donnersm/EdisonRadio/Photos/IMG_9378.JPG

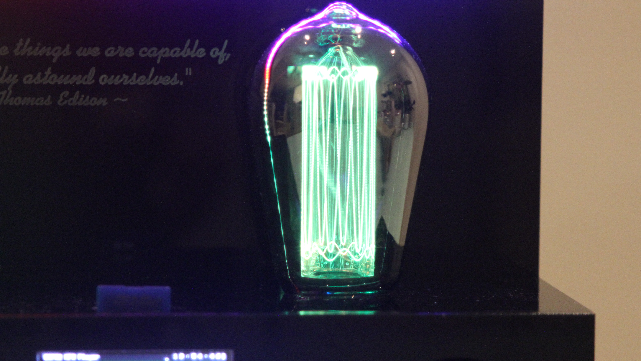
Photos/IMG_9378.JPG
