donnersm/EdisonRadio/Photos/IMG_9388.JPG

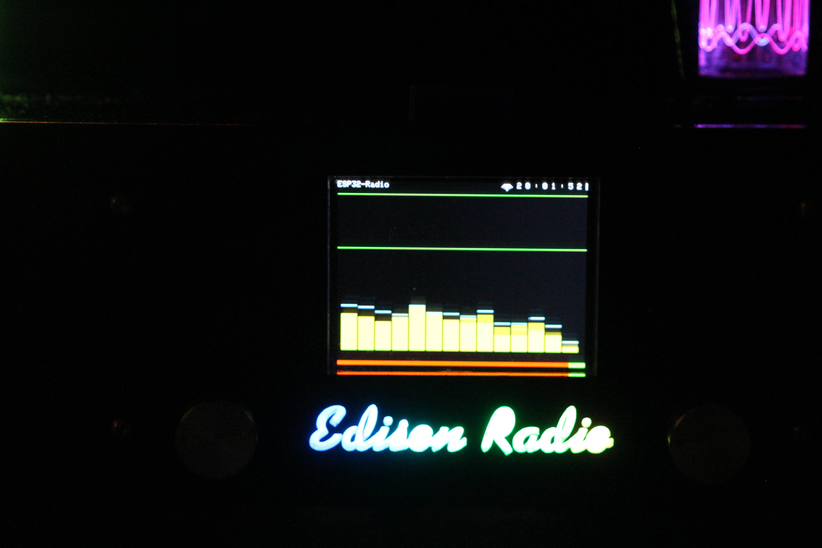
Photos/IMG_9388.JPG
