donnersm/EdisonRadio/Photos/IMG_9389.JPG

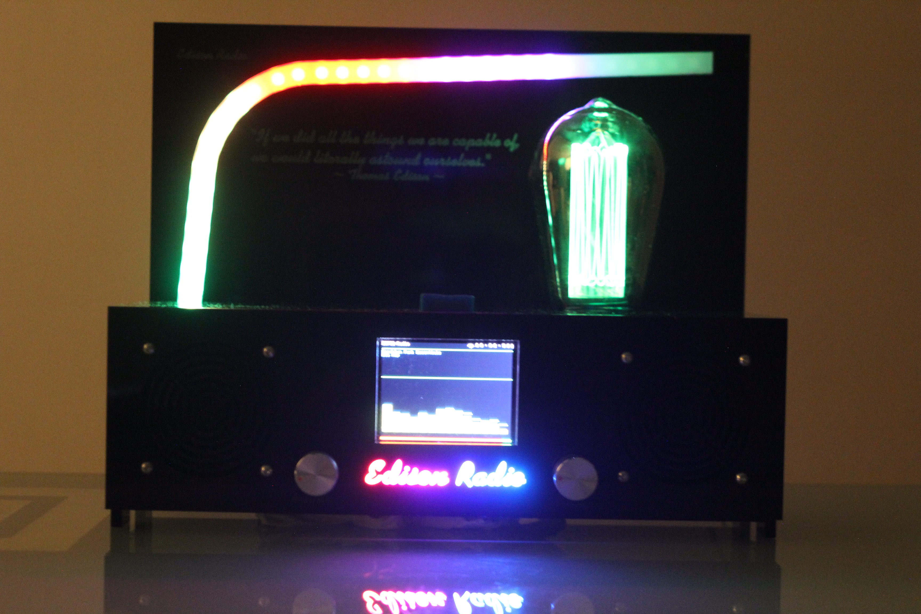
Photos/IMG_9389.JPG
