donnersm/EdisonRadio/Photos/IMG_9398.JPG

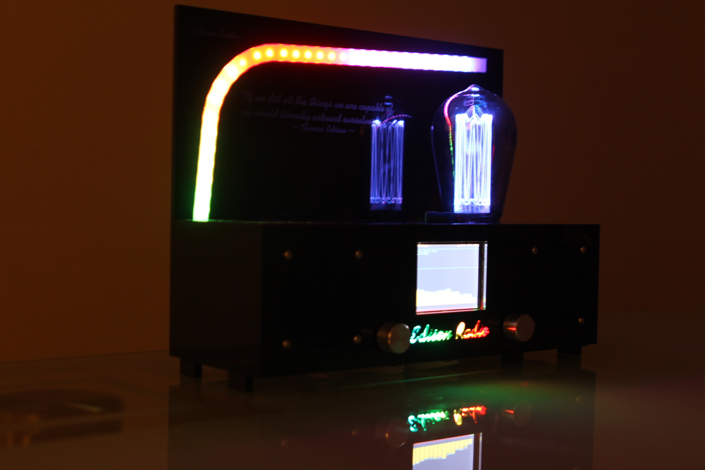
Photos/IMG_9398.JPG
