donnersm/EdisonRadio/Photos/IMG_9399.JPG

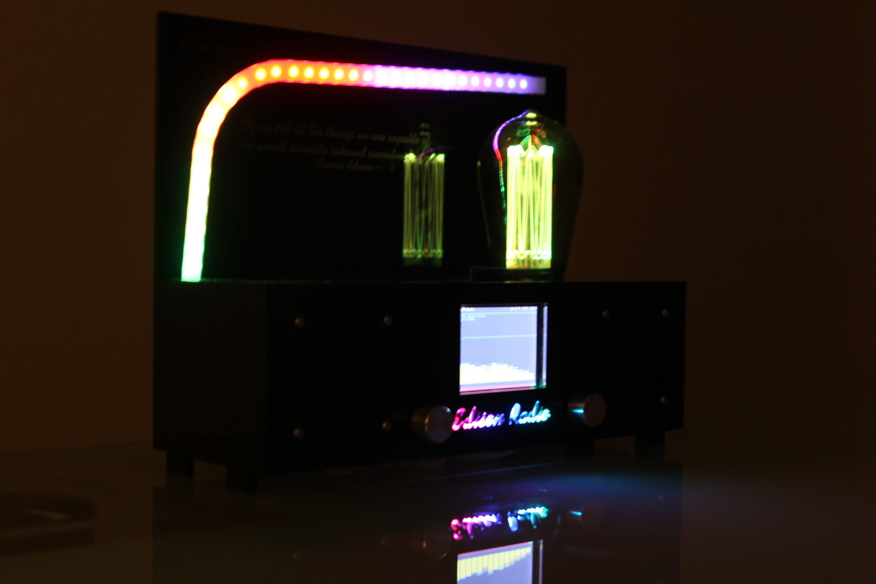
Photos/IMG_9399.JPG
