donnersm/EdisonRadio/ArduinoSketch/MainProgram/ESP32_Radio/ESP32_Radio.ino

//***************************************************************************************************
//*  ESP32_Radio -- Webradio receiver for ESP32, VS1053 MP3 module and optional display.            *
//*                 By Ed Smallenburg.                                                              *
//***************************************************************************************************
//*    Modified according to GNU GENERAL PUBLIC LICENSE to my needs                                 *
//*    Mark Donners AKA  The Electronic Engineer                                                    *
//*    www.thelectronicengineer.nl                                                                  *
//***************************************************************************************************
//
// ESP32 libraries used:
//  - WiFiMulti
//  - nvs
//  - Adafruit_ST7735
//  - ArduinoOTA
//  - PubSubClientenc_dt_pin
//  - SD
//  - FS
//  - update
// A library for the VS1053 (for ESP32) is not available (or not easy to find).  Therefore
// a class for this module is derived from the maniacbug library and integrated in this sketch.
//
// See http://www.internet-radio.com for suitable stations.  Add the stations of your choice
// to the preferences in either Esp32_radio_init.ino sketch or through the webinterface.
//
// Brief description of the program:
// First a suitable WiFi network is found and a connection is made.
// Then a connection will be made to a shoutcast server.  The server starts with some
// info in the header in readable ascii, ending with a double CRLF, like:
//  icy-name:Classic Rock Florida - SHE Radio
//  icy-genre:Classic Rock 60s 70s 80s Oldies Miami South Florida
//  icy-url:http://www.ClassicRockFLorida.com
//  content-type:audio/mpeg
//  icy-pub:1
//  icy-metaint:32768          - Metadata after 32768 bytes of MP3-data
//  icy-br:128                 - in kb/sec (for Ogg this is like "icy-br=Quality 2"
//
// After de double CRLF is received, the server starts sending mp3- or Ogg-data.  For mp3, this
// data may contain metadata (non mp3) after every "metaint" mp3 bytes.
// The metadata is empty in most cases, but if any is available the content will be
// presented on the TFT.
// Pushing an input button causes the player to execute a programmable command.
//
// The display used is a Chinese 1.8 color TFT module 128 x 160 pixels.
// Now there is room for 26 characters per line and 16 lines.
// Software will work without installing the display.
// Other displays are also supported. See documentation.
// The SD card interface of the module may be used to play mp3-tracks on the SD card.
//
// For configuration of the WiFi network(s): see the global data section further on.
//
// The VSPI interface is used for VS1053, TFT and SD.
//
// Wiring. Note that this is just an example.  Pins (except 18,19 and 23 of the SPI interface)
// can be configured in the config page of the web interface.
// ESP32dev Signal  Wired to LCD        Wired to VS1053      SDCARD   Wired to the rest
// -------- ------  --------------      -------------------  ------   ---------------
// GPIO32           -                   pin 1 XDCS            -       -
// GPIO5            -                   pin 2 XCS             -       -
// GPIO4            -                   pin 4 DREQ            -       -
// GPIO2            pin 3 D/C or A0     -                     -       -
// GPIO22           -                   -                     CS      -
// GPIO16   RXD2    -                   -                     -       TX of NEXTION (if in use)
// GPIO17   TXD2    -                   -                     -       RX of NEXTION (if in use)
// GPIO18   SCK     pin 5 CLK or SCK    pin 5 SCK             CLK     -
// GPIO19   MISO    -                   pim           MISO    -
// GPIO23   MOSI    pin 4 DIN or SDA    pin 6 MOSI            MOSI    -
// GPIO15           pin 2 CS            -                     -       -
// GPI03    RXD0    -                   -                     -       Reserved serial input
// GPIO1    TXD0    -                   -                     -       Reserved serial output
// GPIO34   -       -                   -                     -       Optional pull-up resistor
// GPIO35   -       -                   -                     -       Infrared receiver VS1838B
// GPIO25   -       -                   -                     -       Rotary encoder CLK
// GPIO26   -       -                   -                     -       Rotary encoder DT
// GPIO27   -       -                   -                     -       Rotary encoder SW
// -------  ------  ---------------     -------------------  ------   ----------------
// GND      -       pin 8 GND           pin 8 GND                     Power supply GND
// VCC 5 V  -       pin 7 BL            -                             Power supply
// VCC 5 V  -       pin 6 VCC           pin 9 5V                      Power supply
// EN       -       pin 1 RST           pin 3 XRST                    -
//
// 26-04-2017, ES: First set-up, derived from ESP8266 version.
// 08-05-2017, ES: Handling of preferences.
// 20-05-2017, ES: Handling input buttons and MQTT.
// 22-05-2017, ES: Save preset, volume and tone settings.
// 23-05-2017, ES: No more calls of non-iram functions on interrupts.
// 24-05-2017, ES: Support for featherboard.
// 26-05-2017, ES: Correction playing from .m3u playlist. Allow single hidden SSID.
// 30-05-2017, ES: Add SD card support (FAT format), volume indicator.
// 26-06-2017, ES: Correction: start in AP-mode if no WiFi networks configured.
// 28-06-2017, ES: Added IR interface.
// 30-06-2017, ES: Improved functions for SD card play.
// 03-07-2017, ES: Webinterface control page shows current settings.
// 04-07-2017, ES: Correction MQTT subscription. Keep playing during long operations.
// 08-07-2017, ES: More space for streamtitle on TFT.
// 18-07-2017, ES: Time Of Day on TFT.
// 19-07-2017, ES: Minor corrections.
// 26-07-2017, ES: Flexible pin assignment. Add rotary encoder switch.
// 27-07-2017, ES: Removed tinyXML library.
// 18-08-2017, Es: Minor corrections
// 28-08-2017, ES: Preferences for pins used for SPI bus,
//                 Corrected bug in handling programmable pins,
//                 Introduced touch pins.
// 30-08-2017, ES: Limit number of retries for MQTT connection.
//                 Added MDNS responder.
// 11-11-2017, ES: Increased ringbuffer.  Measure bit rate.
// 13-11-2017, ES: Forward declarations.
// 16-11-2017, ES: Replaced ringbuffer by FreeRTOS queue, play function on second CPU,
//                 Included improved rotary switch routines supplied by fenyvesi,
//                 Better IR sensitivity.
// 30-11-2017, ES: Hide passwords in config page.
// 01-12-2017, ES: Better handling of playlist.
// 07-12-2017, ES: Faster handling of config screen.
// 08-12-2017, ES: More MQTT items to publish, added pin_shutdown.
// 13-12-2017, ES: Correction clear LCD.
// 15-12-2017, ES: Correction defaultprefs.h.
// 18-12-2017, ES: Stop playing during config.
// 02-01-2018, ES: Stop/resume is same command.
// 22-01-2018, ES: Read ADC (GPIO36) and display as a battery capacity percentage.
// 13-02-2018, ES: Stop timer during NVS write.
// 15-02-2018, ES: Correction writing wifi credentials in NVS.
// 03-03-2018, ES: Correction bug IR pinnumber.
// 05-03-2018, ES: Improved rotary encoder interface.
// 10-03-2018, ES: Minor corrections.
// 13-04-2018, ES: Guard against empty string send to TFT, thanks to Andreas Spiess.
// 16-04-2018, ES: ID3 tags handling while playing from SD.
// 25-04-2018, ES: Choice of several display boards.
// 30-04-2018, ES: Bugfix: crash when no IR is configured, no display without VS1063.
// 08-05-2018, ES: 1602 LCD display support (limited).
// 11-05-2018, ES: Bugfix: incidental crash in isr_enc_turn().
// 30-05-2018, ES: Bugfix: Assigned DRAM to global variables used in timer ISR.
// 31-05-2018, ES: Bugfix: Crashed if I2C is used, but pins not defined.
// 01-06-2018, ES: Run Playtask on CPU 0.
// 04-06-2018, ES: Made handling of playlistdata more tolerant (NDR).
// 09-06-2018, ES: Typo in defaultprefs.h.
// 10-06-2018, ES: Rotary encoder, interrupts on all 3 signals.
// 25-06-2018, ES: Timing of mp3loop.  Limit read from stream to free queue space.
// 16-07-2018, ES: Correction tftset().
// 25-07-2018, ES: Correction touch pins.
// 30-07-2018, ES: Added GPIO39 and inversed shutdown pin.  Thanks to fletsche.
// 31-07-2018, ES: Added TFT backlight control.
// 01-08-2018, ES: Debug info for IR.  Shutdown amplifier if volume is 0.
// 02-08-2018, ES: Added support for ILI9341 display.
// 03-08-2018, ES: Added playlistposition for MQTT.
// 06-08-2018, ES: Correction negative time offset, OTA through remote host.
// 16-08-2018, ES: Added Nextion support.
// 18-09-2018, ES: "uppreset" and "downpreset" for MP3 player.
// 04-10-2018, ES: Fixed compile error OLED 64x128 display.
// 09-10-2018, ES: Bug fix xSemaphoreTake.
// 05-01-2019, ES: Fine tune datarate.
// 05-01-2019, ES: Basic http authentication. (just one user)
// 11-02-2019, ES: MQTT topic and subtopic size enlarged.
// 24-04-2019, ES: Do not lock SPI during gettime().  Calling gettime may take a long time.
// 15-05-2019, ES: MAX number of presets as a defined constant.
// 16-12-2019, ES: Modify of claimSPI() function for debugability.
// 21-12-2019, ES: Check chip version.
// 23-03-2020, ES: Allow playlists on SD card.
// 25-03-2020, ES: End of playlist: start over.
// 09-07-2020, ES: Add CH376 support.
// 14-07-2020, ES: Dynamic status display in webinterface.
// 17-09-2020, ES: Support for LCD2004. Thanks to mrohner.
// 30-09-2020, ES: Ready for ch376msc library Version 1.4.4
// 14-10-2020, ES: Clear artist and title on new station connect
// 19-10-2020, ES: Fixed LCD2004 errror
//***************************************************************************************************
// 16-12-2020 Code takeover modified last version from ES and combined it with code form LOTFI:   
//            Spectrum Analyzer, changed width volume bar, implemented a search tab to find stations
//
// Define the version number, also used for webserver as Last-Modified header and to
// check version for update.  The format must be exactly as specified by the HTTP standard!
#define VERSION     "Wed, 03 Feb 2021 21:16:00 GMT"
// ESP32-Radio can be updated (OTA) to the latest version from a remote server.
// The download uses the following server and files:
#define UPDATEHOST  "judoles.nl"                    // Host for software updates
#define BINFILE     "/Arduino/Esp32_radio.ino.bin"      // Binary file name for update software
#define TFTFILE     "/Arduino/ESP32-Radio.tft"          // Binary file name for update NEXTION image
//
// Define type of local filesystem(s).  See documentation.
//#define CH376                          // For CXH376 support (reading files from USB stick)
#define SDCARD                         // For SD card support (reading files from SD card)
// Define (just one) type of display.  See documentation.
//#define BLUETFT                        // Works also for RED TFT 128x160
//#define OLED                         // 64x128 I2C OLED
//#define DUMMYTFT                     // Dummy display
//#define LCD1602I2C                   // LCD 1602 display with I2C backpack
//#define LCD2004I2C                   // LCD 2004 display with I2C backpack
#define ILI9341                      // ILI9341 240*320
//#define NEXTION                      // Nextion display. Uses UART 2 (pin 16 and 17)
//#include<FastLED.h>//
#include <Adafruit_NeoPixel.h>
#include <nvs.h>
#include <PubSubClient.h>
#include <WiFiMulti.h>
#include <ESPmDNS.h>
#include <time.h>
#include <stdio.h>
#include <string.h>
#include <SPI.h>
#include <ArduinoOTA.h>
#include <freertos/queue.h>
#include <freertos/task.h>
#include <esp_task_wdt.h>
#include <esp_partition.h>
#include <driver/adc.h>192
#include <Update.h>
#include <base64.h>
#include "logos.h"


// Number of entries in the queue
#define QSIZ 400
// Debug buffer size
#define DEBUG_BUFFER_SIZE 150
#define NVSBUFSIZE 150
// Access point name if connection to WiFi network fails.  Also the hostname for WiFi and OTA.
// Note that the password of an AP must be at least as long as 8 characters.
// Also used for other naming.
#define NAME "ESP32Radio"
// Max number of presets in preferences
#define MAXPRESETS 200
// Maximum number of MQTT reconnects before give-up
#define MAXMQTTCONNECTS 5
// Adjust size of buffer to the longest expected string for nvsgetstr
#define NVSBUFSIZE 150
// Position (column) of time in topline relative to end
#define TIMEPOS -90 //-52
// SPI speed for SD card
#define SDSPEED 1000000
// Size of metaline buffer
#define METASIZ 1024
// Max. number of NVS keys in table
#define MAXKEYS 200
// Time-out [sec] for blanking TFT display (BL pin)
#define BL_TIME 45
//
// Subscription topics for MQTT.  The topic will be pefixed by "PREFIX/", where PREFIX is replaced
// by the the mqttprefix in the preferences.  The next definition will yield the topic
// "ESP32Radio/command" if mqttprefix is "ESP32Radio".
#define MQTT_SUBTOPIC     "command"           // Command to receive from MQTT
//
#define otaclient mp3client                   // OTA uses mp3client for connection to host

//**************************************************************************************************
// Forward declaration and prototypes of various functions.                                        *
//**************************************************************************************************
void        displaytime ( const char* str, uint16_t color = 0xFFFF ) ;
void        showstreamtitle ( const char* ml, bool full = false ) ;
void        handlebyte_ch ( uint8_t b ) ;
void        handleFSf ( const String& pagename ) ;
void        handleCmd()  ;
char*       dbgprint( const char* format, ... ) ;
const char* analyzeCmd ( const char* str ) ;
const char* analyzeCmd ( const char* par, const char* val ) ;
void        chomp ( String &str ) ;
String      httpheader ( String contentstype ) ;
bool        nvssearch ( const char* key ) ;
void        mp3loop() ;
void        stop_mp3client () ;
void        tftlog ( const char *str ) ;
void        tftset ( uint16_t inx, const char *str ) ;
void        tftset ( uint16_t inx, String& str ) ;
void        playtask ( void * parameter ) ;       // Task to play the stream
void        spftask ( void * parameter ) ;        // Task for special functions
void        gettime() ;
void        reservepin ( int8_t rpinnr ) ;
void        claimSPI ( const char* p ) ;          // Claim SPI bus for exclusive access
void        releaseSPI() ;                        // Release the claim
char        utf8ascii ( char ascii ) ;            // Convert UTF8 char to normal char
void        utf8ascii_ip ( char* s ) ;            // In place conversion full string
String      utf8ascii ( const char* s ) ;
uint32_t    ssconv ( const uint8_t* bytes ) ;


//**************************************************************************************************
// Several structs and enums.                                                                      *
//**************************************************************************************************
//

enum fs_type { FS_USB, FS_SD } ;                      // USB- or SD interface

struct scrseg_struct                                  // For screen segments
{
  bool     update_req ;                               // Request update of screen
  uint16_t color ;                                    // Textcolor
  uint16_t y ;                                        // Begin of segment row
  uint16_t height ;                                   // Height of segment
  String   str ;                                      // String to be displayed
} ;

enum qdata_type { QDATA, QSTARTSONG, QSTOPSONG } ;    // datatyp in qdata_struct
struct qdata_struct
{
  int datatyp ;                                       // Identifier
  __attribute__((aligned(4))) uint8_t buf[32] ;       // Buffer for chunk
} ;

struct ini_struct
{
  String         mqttbroker ;                         // The name of the MQTT broker server
  String         mqttprefix ;                         // Prefix to use for topics
  uint16_t       mqttport ;                           // Port, default 1883
  String         mqttuser ;                           // User for MQTT authentication
  String         mqttpasswd ;                         // Password for MQTT authentication
  uint8_t        reqvol ;                             // Requested volume
  uint8_t        rtone[4] ;                           // Requested bass/treble settings
  int16_t        newpreset ;                          // Requested preset
  String         clk_server ;                         // Server to be used for time of day clock
  int8_t         clk_offset ;                         // Offset in hours with respect to UTC
  int8_t         clk_dst ;                            // Number of hours shift during DST
  int8_t         ir_pin ;                             // GPIO connected to output of IR decoder
  int8_t         enc_clk_pin ;                        // GPIO connected to CLK of rotary encoder
  int8_t         enc_dt_pin ;                         // GPIO connected to DT of rotary encoder
  int8_t         enc_sw_pin ;                         // GPIO connected to SW of rotary encoder
  int8_t         tft_cs_pin ;                         // GPIO connected to CS of TFT screen
  int8_t         tft_dc_pin ;                         // GPIO connected to D/C or A0 of TFT screen
  int8_t         tft_scl_pin ;                        // GPIO connected to SCL of i2c TFT screen
  int8_t         tft_sda_pin ;                        // GPIO connected to SDA of I2C TFT screen
  int8_t         tft_bl_pin ;                         // GPIO to activate BL of display
  int8_t         tft_blx_pin ;                        // GPIO to activate BL of display (inversed logic)
  int8_t         sd_cs_pin ;                          // GPIO connected to CS of SD card
  int8_t         vs_cs_pin ;                          // GPIO connected to CS of VS1053
  int8_t         vs_dcs_pin ;                         // GPIO connected to DCS of VS1053
  int8_t         vs_dreq_pin ;                        // GPIO connected to DREQ of VS1053
  int8_t         vs_shutdown_pin ;                    // GPIO to shut down the amplifier
  int8_t         vs_shutdownx_pin ;                   // GPIO to shut down the amplifier (inversed logic)
  int8_t         spi_sck_pin ;                        // GPIO connected to SPI SCK pin
  int8_t         spi_miso_pin ;                       // GPIO connected to SPI MISO pin
  int8_t         spi_mosi_pin ;                       // GPIO connected to SPI MOSI pin
  int8_t         ch376_cs_pin ;                       // GPIO connected to CH376 SS
  int8_t         ch376_int_pin ;                      // GPIO connected to CH376 INT
  uint16_t       bat0 ;                               // ADC value for 0 percent battery charge
  uint16_t       bat100 ;                             // ADC value for 100 percent battery charge
} ;

struct WifiInfo_t                                     // For list with WiFi info
{
  uint8_t inx ;                                       // Index as in "wifi_00"
  char * ssid ;                                       // SSID for an entry
  char * passphrase ;                                 // Passphrase for an entry
} ;

struct nvs_entry
{
  uint8_t  Ns ;                                       // Namespace ID
  uint8_t  Type ;                                     // Type of value
  uint8_t  Span ;                                     // Number of entries used for this item
  uint8_t  Rvs ;                                      // Reserved, should be 0xFF
  uint32_t CRC ;                                      // CRC
  char     Key[16] ;                                  // Key in Ascii
  uint64_t Data ;                                     // Data in entry
} ;

struct nvs_page                                       // For nvs entries
{ // 1 page is 4096 bytes
  uint32_t  State ;
  uint32_t  Seqnr ;
  uint32_t  Unused[5] ;
  uint32_t  CRC ;
  uint8_t   Bitmap[32] ;
  nvs_entry Entry[126] ;
} ;

struct keyname_t                                      // For keys in NVS
{
  char      Key[16] ;                                 // Max length is 15 plus delimeter
} ;

//**************************************************************************************************
// Global data section.                                                                            *
//**************************************************************************************************
// There is a block ini-data that contains some configuration.  Configuration data is              *
// saved in the preferences by the webinterface.  On restart the new data will                     *
// de read from these preferences.                                                                 *
// Items in ini_block can be changed by commands from webserver/MQTT/Serial.                       *
//**************************************************************************************************

enum display_t { T_UNDEFINED, T_BLUETFT, T_OLED,             // Various types of display
                 T_DUMMYTFT, T_LCD1602I2C, T_LCD2004I2C,
                 T_ILI9341, T_NEXTION } ;

enum datamode_t { INIT = 0x1, HEADER = 0x2, DATA = 0x4,      // State for datastream
                  METADATA = 0x8, PLAYLISTINIT = 0x10,
                  PLAYLISTHEADER = 0x20, PLAYLISTDATA = 0x40,
                  STOPREQD = 0x80, STOPPED = 0x100
                } ;

// Global variables
unsigned long millisbands = 0;
int               DEBUG = 1 ;                            // Debug on/off
int               numSsid ;                              // Number of available WiFi networks
WiFiMulti         wifiMulti ;                            // Possible WiFi networks
ini_struct        ini_block ;                            // Holds configurable data
WiFiServer        cmdserver ( 80 ) ;                     // Instance of embedded webserver, port 80
WiFiClient        mp3client ;                            // An instance of the mp3 client, also used for OTA
WiFiClient        cmdclient ;                            // An instance of the client for commands
WiFiClient        wmqttclient ;                          // An instance for mqtt
PubSubClient      mqttclient ( wmqttclient ) ;           // Client for MQTT subscriber
HardwareSerial*   nxtserial = NULL ;                     // Serial port for NEXTION (if defined)
TaskHandle_t      maintask ;                             // Taskhandle for main task
TaskHandle_t      xplaytask ;                            // Task handle for playtask
TaskHandle_t      xspftask ;                             // Task handle for special functions
SemaphoreHandle_t SPIsem = NULL ;                        // For exclusive SPI usage
hw_timer_t*       timer = NULL ;                         // For timer
char              timetxt[9] ;                           // Converted timeinfo
char              cmd[130] ;                             // Command from MQTT or Serial
uint8_t           tmpbuff[6000] ;                        // Input buffer for mp3 or data stream
QueueHandle_t     dataqueue ;                            // Queue for mp3 datastream
QueueHandle_t     spfqueue ;                             // Queue for special functions
qdata_struct      outchunk ;                             // Data to queue
qdata_struct      inchunk ;                              // Data from queue
uint8_t*          outqp = outchunk.buf ;                 // Pointer to buffer in outchunk
uint32_t          totalcount = 0 ;                       // Counter mp3 data
datamode_t        datamode ;                             // State of datastream
int               metacount ;                            // Number of bytes in metadata
int               datacount ;                            // Counter databytes before metadata
char              metalinebf[METASIZ + 1] ;              // Buffer for metaline/ID3 tags
int16_t           metalinebfx ;                          // Index for metalinebf
String            icystreamtitle ;                       // Streamtitle from metadata
String            icyname ;                              // Icecast station name
String            ipaddress ;                            // Own IP-address
int               bitrate ;                              // Bitrate in kb/sec
int               mbitrate ;                             // Measured bitrate
int               metaint = 0 ;                          // Number of databytes between metadata
int16_t           currentpreset = -1 ;                   // Preset station playing
String            host ;                                 // The URL to connect to or file to play
String            hostmem;                               // used to keep the orignal url in mem, in case of redirect!
String            playlist ;                             // The URL of the specified playlist
bool              hostreq = false ;                      // Request for new host
bool              reqtone = false ;                      // New tone setting requested
bool              muteflag = false ;                     // Mute output
bool              resetreq = false ;                     // Request to reset the ESP32
bool              updatereq = false ;                    // Request to update software from remote host
bool              NetworkFound = false ;                 // True if WiFi network connected
bool              mqtt_on = false ;                      // MQTT in use
String            networks ;                             // Found networks in the surrounding
uint16_t          mqttcount = 0 ;                        // Counter MAXMQTTCONNECTS
int8_t            playingstat = 0 ;                      // 1 if radio is playing (for MQTT)
int16_t           playlist_num = 0 ;                     // Nonzero for selection from playlist
fs_type           usb_sd = FS_USB ;                      // SD or USB interface
uint32_t          mp3filelength ;                        // File length
bool              localfile = false ;                    // Play from local mp3-file or not
bool              chunked = false ;                      // Station provides chunked transfer
int               chunkcount = 0 ;                       // Counter for chunked transfer
String            http_getcmd ;                          // Contents of last GET command
String            http_rqfile ;                          // Requested file
bool              http_response_flag = false ;           // Response required
uint16_t          ir_value = 0 ;                         // IR code
uint32_t          ir_0 = 550 ;                           // Average duration of an IR short pulse
uint32_t          ir_1 = 1650 ;                          // Average duration of an IR long pulse
struct tm         timeinfo ;                             // Will be filled by NTP server
bool              time_req = false ;                     // Set time requested
uint16_t          adcval ;                               // ADC value (battery voltage)
uint32_t          clength ;                              // Content length found in http header
uint32_t          max_mp3loop_time = 0 ;                 // To check max handling time in mp3loop (msec)
int16_t           scanios ;                              // TEST*TEST*TEST
int16_t           scaniocount ;                          // TEST*TEST*TEST
uint16_t          bltimer = 0 ;                          // Backlight time-out counter
display_t         displaytype = T_UNDEFINED ;            // Display type
std::vector<WifiInfo_t> wifilist ;                       // List with wifi_xx info
// nvs stuff
nvs_page                nvsbuf ;                         // Space for 1 page of NVS info
const esp_partition_t*  nvs ;                            // Pointer to partition struct
esp_err_t               nvserr ;                         // Error code from nvs functions
uint32_t                nvshandle = 0 ;                  // Handle for nvs access
uint8_t                 namespace_ID ;                   // Namespace ID found
char                    nvskeys[MAXKEYS][16] ;           // Space for NVS keys
std::vector<keyname_t> keynames ;                        // Keynames in NVS
// Rotary encoder stuff
#define sv DRAM_ATTR static volatile
sv uint16_t       clickcount = 0 ;                       // Incremented per encoder click
sv int16_t        rotationcount = 0 ;                    // Current position of rotary switch
sv uint16_t       enc_inactivity = 0 ;                   // Time inactive
sv bool           singleclick = false ;                  // True if single click detected
sv bool           doubleclick = false ;                  // True if double click detected
sv bool           tripleclick = false ;                  // True if triple click detected
sv bool           longclick = false ;                    // True if longclick detected
enum enc_menu_t { VOLUME, PRESET, TRACK } ;              // State for rotary encoder menu
enc_menu_t        enc_menu_mode = VOLUME ;               // Default is VOLUME mode

// Data to display. There are TFTSECS sections
bool tft_update_req ; // Global update request
uint8_t bands = 14; // Number of bands Spectrum Analyzer
uint8_t prevbands = 0; // Number previous band Spectrum Analyzer
uint8_t spectrum[14][3]; // Array per Spectrum Analyzer
const uint8_t Spectrum_y0 = 150;
const uint8_t Spectrum_hy = 70;

// Vu meter stuff
int Vu_waarde=0; // vu meter
//uint16_t vu_waarden; 
//byte VuL, VuR; 
uint8_t  i;
uint16_t minLvl, maxLvl;
int      n, height;
//*******************************************************************************************
//*******************variables and definitions for VU meter and Logo backlight **************
//*******************************************************************************************
#define N_PIXELS  32  // Number of pixels in strand VUmeter
#define LED_PIN    33  // NeoPixel LED strand is connected to this pin
//#define MIC_PIN   32  // Microphone is attached to this analog pin
#define LED_PIN_LOGO    32  // NeoPixel LED strand is connected to this pin 
#define N_PIXELS_LOGO  12  // Number of pixels in strand
//#define MIC_PIN   32  // Microphone is attached to this analog pin


#define DC_OFFSET  0  // DC offset in mic signal - if unusure, leave 0
#define NOISE     25  // Noise/hum/interference in mic signal 167
#define SAMPLES   50  // Length of buffer for dynamic level adjustment 50
#define TOP       (N_PIXELS +1 ) // Allow dot to go slightly off scale 66
#define PEAK_FALL 6 // Rate of peak falling dot 30
#define PIXBRIGHTNESS 64
#define PIXBRIGHTNESSLOGO 64
#define Brightpin 34

Adafruit_NeoPixel
  strip = Adafruit_NeoPixel(N_PIXELS, LED_PIN, NEO_GRB + NEO_KHZ800);
Adafruit_NeoPixel  
  striplogo = Adafruit_NeoPixel(N_PIXELS_LOGO, LED_PIN_LOGO, NEO_GRB + NEO_KHZ800);
byte
  peak      = 0,      // Used for falling dot 0
  dotCount  = 0,      // Frame counter for delaying dot-falling speed 0
  volCount  = 0;      // Frame counter for storing past volume data 0
int
  vol[SAMPLES],       // Collection of prior volume samples
  lvl       = 5,      // Current "dampened" audio level 5
  minLvlAvg = 0,      // For dynamic adjustment of graph low & high 0
  maxLvlAvg = 20;    // 512

long firstPixelHue = 0; // logo only

//
struct progpin_struct                                    // For programmable input pins
{
  int8_t         gpio ;                                  // Pin number
  bool           reserved ;                              // Reserved for connected devices
  bool           avail ;                                 // Pin is available for a command
  String         command ;                               // Command to execute when activated
                                                         // Example: "uppreset=1"
  bool           cur ;                                   // Current state, true = HIGH, false = LOW
} ;

progpin_struct   progpin[] =                             // Input pins and programmed function
{
  {  0, false, false,  "", false },
  //{  1, true,  false,  "", false },                    // Reserved for TX Serial output
  {  2, false, false,  "", false },
  //{  3, true,  false,  "", false },                    // Reserved for RX Serial input
  {  4, false, false,  "", false },
  {  5, false, false,  "", false },
  //{  6, true,  false,  "", false },                    // Reserved for FLASH SCK
  //{  7, true,  false,  "", false },                    // Reserved for FLASH D0
  //{  8, true,  false,  "", false },                    // Reserved for FLASH D1
  //{  9, true,  false,  "", false },                    // Reserved for FLASH D2
  //{ 10, true,  false,  "", false },                    // Reserved for FLASH D3
  //{ 11, true,  false,  "", false },                    // Reserved for FLASH CMD
  { 12, false, false,  "", false },
  { 13, false, false,  "", false },
  { 14, false, false,  "", false },
  { 15, false, false,  "", false },
  { 16, false, false,  "", false },                      // May be UART 2 RX for Nextion
  { 17, false, false,  "", false },                      // May be UART 2 TX for Nextion
  { 18, false, false,  "", false },                      // Default for SPI CLK
  { 19, false, false,  "", false },                      // Default for SPI MISO
  //{ 20, true,  false,  "", false },                    // Not exposed on DEV board
  { 21, false, false,  "", false },                      // Also Wire SDA
  { 22, false, false,  "", false },                      // Also Wire SCL
  { 23, false, false,  "", false },                      // Default for SPI MOSI
  //{ 24, true,  false,  "", false },                    // Not exposed on DEV board
  { 25, false, false,  "", false },
  { 26, false, false,  "", false },
  { 27, false, false,  "", false },
  //{ 28, true,  false,  "", false },                    // Not exposed on DEV board
  //{ 29, true,  false,  "", false },                    // Not exposed on DEV board
  //{ 30, true,  false,  "", false },                    // Not exposed on DEV board
  //{ 31, true,  false,  "", false },                    // Not exposed on DEV board
  { 32, false, false,  "", false },
  { 33, false, false,  "", false },
  { 34, false, false,  "", false },                      // Note, no internal pull-up
  { 35, false, false,  "", false },                      // Note, no internal pull-up
  //{ 36, true,  false,  "", false },                    // Reserved for ADC battery level
  { 39, false,  false,  "", false },                     // Note, no internal pull-up
  { -1, false, false,  "", false }                       // End of list
} ;

struct touchpin_struct                                   // For programmable input pins
{
  int8_t         gpio ;                                  // Pin number GPIO
  bool           reserved ;                              // Reserved for connected devices
  bool           avail ;                                 // Pin is available for a command
  String         command ;                               // Command to execute when activated
  // Example: "uppreset=1"
  bool           cur ;                                   // Current state, true = HIGH, false = LOW
  int16_t        count ;                                 // Counter number of times low level
} ;
touchpin_struct   touchpin[] =                           // Touch pins and programmed function
{
  {   4, false, false, "", false, 0 },                   // TOUCH0
  {   0, true,  false, "", false, 0 },                   // TOUCH1, reserved for BOOT button
  {   2, false, false, "", false, 0 },                   // TOUCH2
  {  15, false, false, "", false, 0 },                   // TOUCH3
  {  13, false, false, "", false, 0 },                   // TOUCH4
  {  12, false, false, "", false, 0 },                   // TOUCH5
  {  14, false, false, "", false, 0 },                   // TOUCH6
  {  27, false, false, "", false, 0 },                   // TOUCH7
  {  33, false, false, "", false, 0 },                   // TOUCH8
  {  32, false, false, "", false, 0 },                   // TOUCH9
  {  -1, false, false, "", false, 0 }                    // End of list
  // End of table
} ;



// declare the LED array
//CRGB leds[N_PIXELS];

// define the variables needed for the audio levels
//int lvl = 0, minLvl = 0, maxLvl = 35; // tweak the min and max as needed

// instantiate the filter class for smoothing the raw audio signal
//ExponentialFilter<long> ADCFilter(5,0);

//**************************************************************************************************
// Pages, CSS and data for the webinterface.                                                       *
//**************************************************************************************************
#include "about_html.h"
#include "config_html.h"
#include "index_html.h"
#include "mp3play_html.h"
#include "find_html.h"
#include "radio_css.h"
#include "favicon_ico.h"
#include "defaultprefs.h"


#include "patches.h"

//**************************************************************************************************
// End of global data section.                                                                     *
//**************************************************************************************************




//**************************************************************************************************
//                                     M Q T T P U B _ C L A S S                                   *
//**************************************************************************************************
// ID's for the items to publish to MQTT.  Is index in amqttpub[]
enum { MQTT_IP,     MQTT_ICYNAME, MQTT_STREAMTITLE, MQTT_NOWPLAYING,
       MQTT_PRESET, MQTT_VOLUME, MQTT_PLAYING, MQTT_PLAYLISTPOS
     } ;
enum { MQSTRING, MQINT8, MQINT16 } ;                     // Type of variable to publish

class mqttpubc                                           // For MQTT publishing
{
    struct mqttpub_struct
    {
      const char*    topic ;                             // Topic as partial string (without prefix)
      uint8_t        type ;                              // Type of payload
      void*          payload ;                           // Payload for this topic
      bool           topictrigger ;                      // Set to true to trigger MQTT publish
    } ;
    // Publication topics for MQTT.  The topic will be pefixed by "PREFIX/", where PREFIX is replaced
    // by the the mqttprefix in the preferences.
  protected:
    mqttpub_struct amqttpub[9] =                   // Definitions of various MQTT topic to publish
    { // Index is equal to enum above
      { "ip",              MQSTRING, &ipaddress,        false }, // Definition for MQTT_IP
      { "icy/name",        MQSTRING, &icyname,          false }, // Definition for MQTT_ICYNAME
      { "icy/streamtitle", MQSTRING, &icystreamtitle,   false }, // Definition for MQTT_STREAMTITLE
      { "nowplaying",      MQSTRING, &ipaddress,        false }, // Definition for MQTT_NOWPLAYING
      { "preset" ,         MQINT8,   &currentpreset,    false }, // Definition for MQTT_PRESET
      { "volume" ,         MQINT8,   &ini_block.reqvol, false }, // Definition for MQTT_VOLUME
      { "playing",         MQINT8,   &playingstat,      false }, // Definition for MQTT_PLAYING
      { "playlist/pos",    MQINT16,  &playlist_num,     false }, // Definition for MQTT_PLAYLISTPOS
      { NULL,              0,        NULL,              false }  // End of definitions
    } ;
  public:
    void          trigger ( uint8_t item ) ;                      // Trigger publishig for one item
    void          publishtopic() ;                                // Publish triggerer items
} ;


//**************************************************************************************************
// MQTTPUB  class implementation.                                                                  *
//**************************************************************************************************

//**************************************************************************************************
//                                            T R I G G E R                                        *
//**************************************************************************************************
// Set request for an item to publish to MQTT.                                                     *
//**************************************************************************************************
void mqttpubc::trigger ( uint8_t item )                    // Trigger publishig for one item
{
  amqttpub[item].topictrigger = true ;                     // Request re-publish for an item
}

//**************************************************************************************************
//                                     P U B L I S H T O P I C                                     *
//**************************************************************************************************
// Publish a topic to MQTT broker.                                                                 *
//**************************************************************************************************
void mqttpubc::publishtopic()
{
  int         i = 0 ;                                         // Loop control
  char        topic[80] ;                                     // Topic to send
  const char* payload ;                                       // Points to payload
  char        intvar[10] ;                                    // Space for integer parameter
  while ( amqttpub[i].topic )
  {
    if ( amqttpub[i].topictrigger )                           // Topic ready to send?
    {
      amqttpub[i].topictrigger = false ;                      // Success or not: clear trigger
      sprintf ( topic, "%s/%s", ini_block.mqttprefix.c_str(),
                amqttpub[i].topic ) ;                         // Add prefix to topic
      switch ( amqttpub[i].type )                             // Select conversion method
      {
        case MQSTRING :
          payload = ((String*)amqttpub[i].payload)->c_str() ;
          //payload = pstr->c_str() ;                           // Get pointer to payload
          break ;
        case MQINT8 :
          sprintf ( intvar, "%d",
                    *(int8_t*)amqttpub[i].payload ) ;         // Convert to array of char
          payload = intvar ;                                  // Point to this array
          break ;
        case MQINT16 :
          sprintf ( intvar, "%d",
                    *(int16_t*)amqttpub[i].payload ) ;        // Convert to array of char
          payload = intvar ;                                  // Point to this array
          break ;
        default :
          continue ;                                          // Unknown data type
      }
      dbgprint ( "Publish to topic %s : %s",                  // Show for debug
                 topic, payload ) ;
      if ( !mqttclient.publish ( topic, payload ) )           // Publish!
      {
        dbgprint ( "MQTT publish failed!" ) ;                 // Failed
      }
      return ;                                                // Do the rest later
    }
    i++ ;                                                     // Next entry
  }
}

mqttpubc         mqttpub ;                                    // Instance for mqttpubc


//
//**************************************************************************************************
// VS1053 stuff.  Based on maniacbug library.                                                      *
//**************************************************************************************************
// VS1053 class definition.                                                                        *
//**************************************************************************************************
class VS1053
{
  private:
    int8_t        cs_pin ;                         // Pin where CS line is connected
    int8_t        dcs_pin ;                        // Pin where DCS line is connected
    int8_t        dreq_pin ;                       // Pin where DREQ line is connected
    int8_t        shutdown_pin ;                   // Pin where the shutdown line is connected
    int8_t        shutdownx_pin ;                  // Pin where the shutdown (inversed) line is connected
    uint8_t       curvol ;                         // Current volume setting 0..100%
    const uint8_t vs1053_chunk_size = 32 ;
    // SCI Register
    const uint8_t SCI_MODE          = 0x0 ;
    const uint8_t SCI_STATUS        = 0x1 ;
    const uint8_t SCI_BASS          = 0x2 ;
    const uint8_t SCI_CLOCKF        = 0x3 ;
    const uint8_t SCI_AUDATA        = 0x5 ;
    const uint8_t SCI_WRAM          = 0x6 ;
    const uint8_t SCI_WRAMADDR      = 0x7 ;
    const uint8_t SCI_AIADDR        = 0xA ;
    const uint8_t SCI_VOL           = 0xB ;
    const uint8_t SCI_AICTRL0       = 0xC ;
    const uint8_t SCI_AICTRL1       = 0xD ;
    const uint8_t SCI_num_registers = 0xF ;
    // SCI_MODE bits
    const uint8_t SM_SDINEW         = 11 ;        // Bitnumber in SCI_MODE always on
    const uint8_t SM_RESET          = 2 ;         // Bitnumber in SCI_MODE soft reset
    const uint8_t SM_CANCEL         = 3 ;         // Bitnumber in SCI_MODE cancel song
    const uint8_t SM_TESTS          = 5 ;         // Bitnumber in SCI_MODE for tests
    const uint8_t SM_LINE1          = 14 ;        // Bitnumber in SCI_MODE for Line input
    SPISettings   VS1053_SPI ;                    // SPI settings for this slave
    uint8_t       endFillByte ;                   // Byte to send when stopping song
    bool          okay              = true ;      // VS1053 is working
  protected:
    inline void await_data_request() const
    { short pseu=1;
      while ( ( dreq_pin >= 0 ) &&
              ( !digitalRead ( dreq_pin ) ) )
      {
    //    NOP() ;                                   // Very short delay doesnt work in combi with fastlib library
    
    pseu=0;                                       //instead replace by pseudo commmand: resetting a short integer.
      }
    }

    inline void control_mode_on() const
    {
      SPI.beginTransaction ( VS1053_SPI ) ;       // Prevent other SPI users
      digitalWrite ( cs_pin, LOW ) ;
    }

    inline void control_mode_off() const
    {
      digitalWrite ( cs_pin, HIGH ) ;             // End control mode
      SPI.endTransaction() ;                      // Allow other SPI users
    }

    inline void data_mode_on() const
    {
      SPI.beginTransaction ( VS1053_SPI ) ;       // Prevent other SPI users
      //digitalWrite ( cs_pin, HIGH ) ;           // Bring slave in data mode
      digitalWrite ( dcs_pin, LOW ) ;
    }

    inline void data_mode_off() const
    {
      digitalWrite ( dcs_pin, HIGH ) ;            // End data mode
      SPI.endTransaction() ;                      // Allow other SPI users
    }

    uint16_t    read_register ( uint8_t _reg ) const ;
    void        write_register ( uint8_t _reg, uint16_t _value ) const ;
    inline bool sdi_send_buffer ( uint8_t* data, size_t len ) ;
    void        sdi_send_fillers ( size_t length ) ;
    void        wram_write ( uint16_t address, uint16_t data ) ;
    uint16_t    wram_read ( uint16_t address ) ;
    void        output_enable ( bool ena ) ;             // Enable amplifier through shutdown pin(s)

  public:
    // Constructor.  Only sets pin values.  Doesn't touch the chip.  Be sure to call begin()!
    VS1053 ( int8_t _cs_pin, int8_t _dcs_pin, int8_t _dreq_pin,
             int8_t _shutdown_pin, int8_t _shutdownx_pin ) ;
    void     begin() ;                                   // Begin operation.  Sets pins correctly,
    // and prepares SPI bus.
    void     startSong() ;                               // Prepare to start playing. Call this each
    // time a new song starts.
    inline bool playChunk ( uint8_t* data,               // Play a chunk of data.  Copies the data to
                            size_t len ) ;               // the chip.  Blocks until complete.
    // Returns true if more data can be added
    // to fifo
    void     stopSong() ;                                // Finish playing a song. Call this after
    // the last playChunk call.
    void     setVolume ( uint8_t vol ) ;                 // Set the player volume.Level from 0-100,
    // higher is louder.
    void     setTone ( uint8_t* rtone ) ;                // Set the player baas/treble, 4 nibbles for
    // treble gain/freq and bass gain/freq
    inline uint8_t  getVolume() const                    // Get the current volume setting.
    { // higher is louder.
      return curvol ;
    }
    void     printDetails ( const char *header ) ;       // Print config details to serial output
    void     softReset() ;                               // Do a soft reset
    bool     testComm ( const char *header ) ;           // Test communication with module
    inline bool data_request() const
    {
      return ( digitalRead ( dreq_pin ) == HIGH ) ;
    }
    void     AdjustRate ( long ppm2 ) ;                  // Fine tune the datarate
    void LoadUserCode( const unsigned short * iplugin, uint16_t sizea);
    inline void getBands();
   
} ;

//**************************************************************************************************
// VS1053 class implementation.                                                                    *
//**************************************************************************************************

VS1053::VS1053 ( int8_t _cs_pin, int8_t _dcs_pin, int8_t _dreq_pin,
                 int8_t _shutdown_pin, int8_t _shutdownx_pin ) :
  cs_pin(_cs_pin), dcs_pin(_dcs_pin), dreq_pin(_dreq_pin), shutdown_pin(_shutdown_pin),
  shutdownx_pin(_shutdownx_pin)
{
}

uint16_t VS1053::read_register ( uint8_t _reg ) const
{
  uint16_t result ;

  control_mode_on() ;
  SPI.write ( 3 ) ;                                // Read operation
  SPI.write ( _reg ) ;                             // Register to write (0..0xF)
  // Note: transfer16 does not seem to work
  result = ( SPI.transfer ( 0xFF ) << 8 ) |        // Read 16 bits data
           ( SPI.transfer ( 0xFF ) ) ;
  await_data_request() ;                           // Wait for DREQ to be HIGH again
  control_mode_off() ;
  return result ;
}

void VS1053::write_register ( uint8_t _reg, uint16_t _value ) const
{
  control_mode_on( );
  SPI.write ( 2 ) ;                                // Write operation
  SPI.write ( _reg ) ;                             // Register to write (0..0xF)
  SPI.write16 ( _value ) ;                         // Send 16 bits data
  await_data_request() ;
  control_mode_off() ;
}

bool VS1053::sdi_send_buffer ( uint8_t* data, size_t len )
{
  size_t chunk_length ;                            // Length of chunk 32 byte or shorter

  data_mode_on() ;
  while ( len )                                    // More to do?
  {
    chunk_length = len ;
    if ( len > vs1053_chunk_size )
    {
      chunk_length = vs1053_chunk_size ;
    }
    len -= chunk_length ;
    await_data_request() ;                         // Wait for space available
    SPI.writeBytes ( data, chunk_length ) ;
    data += chunk_length ;
  }
  data_mode_off() ;
  return data_request() ;                          // True if more data can de stored in fifo
}

void VS1053::sdi_send_fillers ( size_t len )
{
  size_t chunk_length ;                            // Length of chunk 32 byte or shorter

  data_mode_on() ;
  while ( len )                                    // More to do?
  {
    await_data_request() ;                         // Wait for space available
    chunk_length = len ;
    if ( len > vs1053_chunk_size )
    {
      chunk_length = vs1053_chunk_size ;
    }
    len -= chunk_length ;
    while ( chunk_length-- )
    {
      SPI.write ( endFillByte ) ;
    }
  }
  data_mode_off();
}

void VS1053::wram_write ( uint16_t address, uint16_t data )
{
  write_register ( SCI_WRAMADDR, address ) ;
  write_register ( SCI_WRAM, data ) ;
}

uint16_t VS1053::wram_read ( uint16_t address )
{
  write_register ( SCI_WRAMADDR, address ) ;            // Start reading from WRAM
  return read_register ( SCI_WRAM ) ;                   // Read back result
}

bool VS1053::testComm ( const char *header )
{
  // Test the communication with the VS1053 module.  The result wille be returned.
  // If DREQ is low, there is problably no VS1053 connected.  Pull the line HIGH
  // in order to prevent an endless loop waiting for this signal.  The rest of the
  // software will still work, but readbacks from VS1053 will fail.
  int            i ;                                    // Loop control
  uint16_t       r1, r2, cnt = 0 ;
  uint16_t       delta = 300 ;                          // 3 for fast SPI
  const uint16_t vstype[] = { 1001, 1011, 1002, 1003,   // Possible chip versions
                              1053, 1033, 0000, 1103 } ;

  dbgprint ( header ) ;                                 // Show a header
  if ( !digitalRead ( dreq_pin ) )
  {
    dbgprint ( "VS1053 not properly installed!" ) ;
    // Allow testing without the VS1053 module
    pinMode ( dreq_pin,  INPUT_PULLUP ) ;               // DREQ is now input with pull-up
    return false ;                                      // Return bad result
  }
  // Further TESTING.  Check if SCI bus can write and read without errors.
  // We will use the volume setting for this.
  // Will give warnings on serial output if DEBUG is active.
  // A maximum of 20 errors will be reported.
  if ( strstr ( header, "Fast" ) )
  {
    delta = 3 ;                                         // Fast SPI, more loops
  }
  for ( i = 0 ; ( i < 0xFFFF ) && ( cnt < 20 ) ; i += delta )
  {
    write_register ( SCI_VOL, i ) ;                     // Write data to SCI_VOL
    r1 = read_register ( SCI_VOL ) ;                    // Read back for the first time
    r2 = read_register ( SCI_VOL ) ;                    // Read back a second time
    if  ( r1 != r2 || i != r1 || i != r2 )              // Check for 2 equal reads
    {
      dbgprint ( "VS1053 SPI error. SB:%04X R1:%04X R2:%04X", i, r1, r2 ) ;
      cnt++ ;
      delay ( 10 ) ;
    }
  }
  okay = ( cnt == 0 ) ;                                 // True if working correctly
  // Further testing: is it the right chip?
  r1 = ( read_register ( SCI_STATUS ) >> 4 ) & 0x7 ;    // Read status to get the version
  if ( r1 !=  4 )                                       // Version 4 is a genuine VS1053
  {
    dbgprint ( "This is not a VS1053, "                 // Report the wrong chip
               "but a VS%d instead!",
               vstype[r1] ) ;
    okay = false ;
  }
  return ( okay ) ;                                     // Return the result
}

void VS1053::begin()
{
  pinMode      ( dreq_pin,  INPUT ) ;                   // DREQ is an input
  pinMode      ( cs_pin,    OUTPUT ) ;                  // The SCI and SDI signals
  pinMode      ( dcs_pin,   OUTPUT ) ;
  digitalWrite ( dcs_pin,   HIGH ) ;                    // Start HIGH for SCI en SDI
  digitalWrite ( cs_pin,    HIGH ) ;
 uint16_t status_waarde;
 #define SS_VU_ENABLE 0x0200 // B0000001000000000 (7-de bit van links is 1);  
  if ( shutdown_pin >= 0 )                              // Shutdown in use?
  {
    pinMode ( shutdown_pin,   OUTPUT ) ;
  }
  if ( shutdownx_pin >= 0 )                            // Shutdown (inversed logic) in use?
  {
    pinMode ( shutdownx_pin,   OUTPUT ) ;
  }
  output_enable ( false ) ;                            // Disable amplifier through shutdown pin(s)
  delay ( 100 ) ;
  // Init SPI in slow mode ( 0.2 MHz )
  VS1053_SPI = SPISettings ( 200000, MSBFIRST, SPI_MODE0 ) ;
  SPI.setDataMode ( SPI_MODE0 ) ;
  SPI.setBitOrder ( MSBFIRST ) ;
  //printDetails ( "Right after reset/startup" ) ;
  delay ( 20 ) ;
  //printDetails ( "20 msec after reset" ) ;
  if ( testComm ( "Slow SPI, Testing VS1053 read/write registers..." ) )
  {
    // Most VS1053 modules will start up in midi mode.  The result is that there is no audio
    // when playing MP3.  You can modify the board, but there is a more elegant way:
    wram_write ( 0xC017, 3 ) ;                            // GPIO DDR = 3
    wram_write ( 0xC019, 0 ) ;                            // GPIO ODATA = 0
    delay ( 100 ) ;
    //printDetails ( "After test loop" ) ;
    softReset() ;                                         // Do a soft reset
    // Switch on the analog parts
    write_register ( SCI_AUDATA, 44100 + 1 ) ;            // 44.1kHz + stereo
    // The next clocksetting allows SPI clocking at 5 MHz, 4 MHz is safe then.
    write_register ( SCI_CLOCKF, 6 << 12 ) ;              // Normal clock settings
    // multiplyer 3.0 = 12.2 MHz
    //SPI Clock to 4 MHz. Now you can set high speed SPI clock.
    VS1053_SPI = SPISettings ( 5000000, MSBFIRST, SPI_MODE0 ) ;
    write_register ( SCI_MODE, _BV ( SM_SDINEW ) | _BV ( SM_LINE1 ) ) ;
    testComm ( "Fast SPI, Testing VS1053 read/write registers again..." ) ;
    delay ( 10 ) ;
    await_data_request() ;
    endFillByte = wram_read ( 0x1E06 ) & 0xFF ;
    dbgprint ( "endFillByte is %X", endFillByte ) ;
    //printDetails ( "After last clocksetting" ) ;
    delay ( 100 ) ;
       // LoadUserCode(plugin, PLUGIN_SIZE);
       // delay(100);
    LoadUserCode(analizer, ANALIZER_SIZE);

  }
}
void  VS1053::LoadUserCode( const unsigned short* iplugin, uint16_t sizea) {
    int i = 0;
    int ssize = sizea;
    sizea *= sizeof(iplugin[0]);
    while (i<ssize) {
        unsigned short addr, n, val;
        addr = iplugin[i++];
        n =  iplugin[i++];
        if (n & 0x8000U) { /* RLE run, replicate n samples */
            n &= 0x7FFF;
            val = iplugin[i++];
            while (n--) {
                write_register((uint8_t)addr, (uint16_t)val);
            }
        } else {           /* Copy run, copy n samples */
            while (n--) {
                val = iplugin[i++];
                write_register((uint8_t)addr, (uint16_t)val);
            }
        }
    }
}

// spectrumAnalyzerAppl1053b-2.plg
// results in XRAM 0x1810 .. 0x1877
#define BASE 0x1810
void VS1053::getBands()
{ int VU_tot=0;
    write_register(SCI_WRAMADDR, BASE+2);
    bands = read_register(SCI_WRAM);
    write_register(SCI_WRAMADDR, BASE+4);
    Vu_waarde=0;
    for (uint8_t i = 0; i < 14; i++) {
        uint8_t val = read_register(SCI_WRAM);
        /* current value in bits 5..0, normally 0..31
        peak value in bits 11..6, normally 0..31 */
        uint8_t cur1 = val & 31;
        uint8_t cur = (cur1*curvol)/30; // big bars
        if ( cur < 0 ) cur = 0;
        else if ( cur > (Spectrum_hy-4) ) cur = Spectrum_hy-4;
        spectrum[i][0] = cur; 
        //if (cur>Vu_waarde)Vu_waarde=cur; //werkt maar representatie is niet voldoende
        VU_tot=VU_tot+cur; //werkt maar representatie is niet voldoende
    }
    Vu_waarde=VU_tot;
  //  dbgprint("vuwaarde totaal: %i",Vu_waarde);
  //  Vu_waarde=(spectrum[0][0] + spectrum[3][0] +spectrum[6][0] + spectrum[10][0])/4;
   // Vu_waarde=spectrum[6][0];
}






void VS1053::setVolume ( uint8_t vol )
{
  // Set volume.  Both left and right.
  // Input value is 0..100.  100 is the loudest.
  // Clicking reduced by using 0xf8 to 0x00 as limits.
  uint16_t value ;                                      // Value to send to SCI_VOL

  if ( vol != curvol )
  {
    curvol = vol ;                                      // Save for later use
    value = map ( vol, 0, 100, 0xF8, 0x00 ) ;           // 0..100% to one channel
    value = ( value << 8 ) | value ;
    write_register ( SCI_VOL, value ) ;                 // Volume left and right
    if ( vol == 0 )                                     // Completely silence?
    {
      output_enable ( false ) ;                         // Yes, mute amplifier
    }
    else
    {
      if ( datamode != STOPPED )
      {
      output_enable ( true ) ;                          // Enable amplifier if not stopped
      }
    }
    output_enable ( vol != 0 ) ;                        // Enable/disable amplifier through shutdown pin(s)
  }
}

void VS1053::setTone ( uint8_t *rtone )                 // Set bass/treble (4 nibbles)
{
  // Set tone characteristics.  See documentation for the 4 nibbles.
  uint16_t value = 0 ;                                  // Value to send to SCI_BASS
  int      i ;                                          // Loop control

  for ( i = 0 ; i < 4 ; i++ )
  {
    value = ( value << 4 ) | rtone[i] ;                 // Shift next nibble in
  }
  write_register ( SCI_BASS, value ) ;                  // Volume left and right
}

void VS1053::startSong()
{
  sdi_send_fillers ( 10 ) ;
  output_enable ( true ) ;                              // Enable amplifier through shutdown pin(s)
}

bool VS1053::playChunk ( uint8_t* data, size_t len )
{
  return okay && sdi_send_buffer ( data, len ) ;        // True if more data can be added to fifo
}

void VS1053::stopSong()
{
  uint16_t modereg ;                                    // Read from mode register
  int      i ;                                          // Loop control

  sdi_send_fillers ( 2052 ) ;
  output_enable ( false ) ;                             // Disable amplifier through shutdown pin(s)
  delay ( 10 ) ;
  write_register ( SCI_MODE, _BV ( SM_SDINEW ) | _BV ( SM_CANCEL ) ) ;
  for ( i = 0 ; i < 20 ; i++ )
  {
    sdi_send_fillers ( 32 ) ;
    modereg = read_register ( SCI_MODE ) ;              // Read mode status
    if ( ( modereg & _BV ( SM_CANCEL ) ) == 0 )         // SM_CANCEL will be cleared when finished
    {
      sdi_send_fillers ( 2052 ) ;
      dbgprint ( "Song stopped correctly after %d msec", i * 10 ) ;
      return ;
    }
    delay ( 10 ) ;
  }
  printDetails ( "Song stopped incorrectly!" ) ;
}

void VS1053::softReset()
{
  write_register ( SCI_MODE, _BV ( SM_SDINEW ) | _BV ( SM_RESET ) ) ;
  delay ( 10 ) ;
  await_data_request() ;
}

void VS1053::printDetails ( const char *header )
{
  uint16_t     regbuf[16] ;
  uint8_t      i ;

  dbgprint ( header ) ;
  dbgprint ( "REG   Contents" ) ;
  dbgprint ( "---   -----" ) ;
  for ( i = 0 ; i <= SCI_num_registers ; i++ )
  {
    regbuf[i] = read_register ( i ) ;
  }
  for ( i = 0 ; i <= SCI_num_registers ; i++ )
  {
    delay ( 5 ) ;
    dbgprint ( "%3X - %5X", i, regbuf[i] ) ;
  }
}

void  VS1053::output_enable ( bool ena )               // Enable amplifier through shutdown pin(s)
{
  if ( shutdown_pin >= 0 )                             // Shutdown in use?
  {
    digitalWrite ( shutdown_pin, !ena ) ;              // Shut down or enable audio output
  }
  if ( shutdownx_pin >= 0 )                            // Shutdown (inversed logic) in use?
  {
    digitalWrite ( shutdownx_pin, ena ) ;              // Shut down or enable audio output
  }
}


void VS1053::AdjustRate ( long ppm2 )                  // Fine tune the data rate
{
  write_register ( SCI_WRAMADDR, 0x1e07 ) ;
  write_register ( SCI_WRAM,     ppm2 ) ;
  write_register ( SCI_WRAM,     ppm2 >> 16 ) ;
  // oldClock4KHz = 0 forces  adjustment calculation when rate checked.
  write_register ( SCI_WRAMADDR, 0x5b1c ) ;
  write_register ( SCI_WRAM,     0 ) ;
  // Write to AUDATA or CLOCKF checks rate and recalculates adjustment.
  write_register ( SCI_AUDATA,   read_register ( SCI_AUDATA ) ) ;
}


// The object for the MP3 player
VS1053* vs1053player ;

//**************************************************************************************************
// End VS1053 stuff.                                                                               *
//**************************************************************************************************

// Include software for the right display
#ifdef BLUETFT
#include "bluetft.h"                                     // For ILI9163C or ST7735S 128x160 display
#endif
#ifdef ILI9341
#include "ILI9341.h"                                     // For ILI9341 320x240 display
#endif
#ifdef OLED
#include "SSD1306.h"                                     // For OLED I2C SD1306 64x128 display
#endif
#ifdef LCD1602I2C
#include "LCD1602.h"                                     // For LCD 1602 display (I2C)
#endif
#ifdef LCD2004I2C
#include "LCD2004.h"                                     // For LCD 2004 display (I2C)
#endif
#ifdef DUMMYTFT
#include "Dummytft.h"                                    // For Dummy display
#endif
#ifdef NEXTION
#include "NEXTION.h"                                     // For NEXTION display
#endif
//
// Include software for CH376
#include "CH376.h"                                       // For CH376 USB interface
// Include software for SD card
#include "SDcard.h"                                      // For SD caard interface

//**************************************************************************************************
//                                           B L S E T                                             *
//**************************************************************************************************
// Enable or disable the TFT backlight if configured.                                              *
// May be called from interrupt level.                                                             *
//**************************************************************************************************
void IRAM_ATTR blset ( bool enable )
{
  if ( ini_block.tft_bl_pin >= 0 )                       // Backlight for TFT control?
  {
    digitalWrite ( ini_block.tft_bl_pin, enable ) ;      // Enable/disable backlight
  }
  if ( ini_block.tft_blx_pin >= 0 )                      // Backlight for TFT (inversed logic) control?
  {
    digitalWrite ( ini_block.tft_blx_pin, !enable ) ;    // Enable/disable backlight
  }
  if ( enable )
  {
    bltimer = 0 ;                                        // Reset counter backlight time-out
  }
}


//**************************************************************************************************
//                                      N V S O P E N                                              *
//**************************************************************************************************
// Open Preferences with my-app namespace. Each application module, library, etc.                  *
// has to use namespace name to prevent key name collisions. We will open storage in               *
// RW-mode (second parameter has to be false).                                                     *
//**************************************************************************************************
void nvsopen()
{
  if ( ! nvshandle )                                         // Opened already?
  {
    nvserr = nvs_open ( NAME, NVS_READWRITE, &nvshandle ) ;  // No, open nvs
    if ( nvserr )
    {
      dbgprint ( "nvs_open failed!" ) ;
    }
  }
}


//**************************************************************************************************
//                                      N V S C L E A R                                            *
//**************************************************************************************************
// Clear all preferences.                                                                          *
//**************************************************************************************************
esp_err_t nvsclear()
{
  nvsopen() ;                                         // Be sure to open nvs
  return nvs_erase_all ( nvshandle ) ;                // Clear all keys
}


//**************************************************************************************************
//                                      N V S G E T S T R                                          *
//**************************************************************************************************
// Read a string from nvs.                                                                         *
//**************************************************************************************************
String nvsgetstr ( const char* key )
{
  static char   nvs_buf[NVSBUFSIZE] ;       // Buffer for contents
  size_t        len = NVSBUFSIZE ;          // Max length of the string, later real length

  nvsopen() ;                               // Be sure to open nvs
  nvs_buf[0] = '\0' ;                       // Return empty string on error
  nvserr = nvs_get_str ( nvshandle, key, nvs_buf, &len ) ;
  if ( nvserr )
  {
    dbgprint ( "nvs_get_str failed %X for key %s, keylen is %d, len is %d!",
               nvserr, key, strlen ( key), len ) ;
    dbgprint ( "Contents: %s", nvs_buf ) ;
  }
  return String ( nvs_buf ) ;
}


//**************************************************************************************************
//                                      N V S S E T S T R                                          *
//**************************************************************************************************
// Put a key/value pair in nvs.  Length is limited to allow easy read-back.                        *
// No writing if no change.                                                                        *
//**************************************************************************************************
esp_err_t nvssetstr ( const char* key, String val )
{
  String curcont ;                                         // Current contents
  bool   wflag = true  ;                                   // Assume update or new key

  //dbgprint ( "Setstring for %s: %s", key, val.c_str() ) ;
  if ( val.length() >= NVSBUFSIZE )                        // Limit length of string to store
  {
    dbgprint ( "nvssetstr length failed!" ) ;
    return ESP_ERR_NVS_NOT_ENOUGH_SPACE ;
  }
  if ( nvssearch ( key ) )                                 // Already in nvs?
  {
    curcont = nvsgetstr ( key ) ;                          // Read current value
    wflag = ( curcont != val ) ;                           // Value change?
  }
  if ( wflag )                                             // Update or new?
  {
    //dbgprint ( "nvssetstr update value" ) ;
    nvserr = nvs_set_str ( nvshandle, key, val.c_str() ) ; // Store key and value
    if ( nvserr )                                          // Check error
    {
      dbgprint ( "nvssetstr failed!" ) ;
    }
  }
  return nvserr ;
}


//**************************************************************************************************
//                                      N V S C H K E Y                                            *
//**************************************************************************************************
// Change a keyname in in nvs.                                                                     *
//**************************************************************************************************
void nvschkey ( const char* oldk, const char* newk )
{
  String curcont ;                                         // Current contents

  if ( nvssearch ( oldk ) )                                // Old key in nvs?
  {
    curcont = nvsgetstr ( oldk ) ;                         // Read current value
    nvs_erase_key ( nvshandle, oldk ) ;                    // Remove key
    nvssetstr ( newk, curcont ) ;                          // Insert new
  }
}


//**************************************************************************************************
//                                      C L A I M S P I                                            *
//**************************************************************************************************
// Claim the SPI bus.  Uses FreeRTOS semaphores.                                                   *
// If the semaphore cannot be claimed within the time-out period, the function continues without   *
// claiming the semaphore.  This is incorrect but allows debugging.                                *
//**************************************************************************************************
void claimSPI ( const char* p )
{
  const              TickType_t ctry = 10 ;                 // Time to wait for semaphore
  uint32_t           count = 0 ;                            // Wait time in ticks
  static const char* old_id = "none" ;                      // ID that holds the bus

  while ( xSemaphoreTake ( SPIsem, ctry ) != pdTRUE  )      // Claim SPI bus
  {
    if ( count++ > 25 )
    {
      dbgprint ( "SPI semaphore not taken within %d ticks by CPU %d, id %s",
                 count * ctry,
                 xPortGetCoreID(),
                 p ) ;
      dbgprint ( "Semaphore is claimed by %s", old_id ) ;
    }
    if ( count >= 100 )
    {
      return ;                                               // Continue without semaphore
    }
  }
  old_id = p ;                                               // Remember ID holding the semaphore
}


//**************************************************************************************************
//                                   R E L E A S E S P I                                           *
//**************************************************************************************************
// Free the the SPI bus.  Uses FreeRTOS semaphores.                                                *
//**************************************************************************************************
void releaseSPI()
{
  xSemaphoreGive ( SPIsem ) ;                            // Release SPI bus
}


//**************************************************************************************************
//                                      Q U E U E F U N C                                          *
//**************************************************************************************************
// Queue a special function for the play task.                                                     *
//**************************************************************************************************
void queuefunc ( int func )
{
  qdata_struct     specchunk ;                          // Special function to queue

  specchunk.datatyp = func ;                            // Put function in datatyp
  xQueueSendToFront ( dataqueue, &specchunk, 200 ) ;    // Send to queue (First Out)
}


//**************************************************************************************************
//                                      N V S S E A R C H                                          *
//**************************************************************************************************
// Check if key exists in nvs.                                                                     *
//**************************************************************************************************
bool nvssearch ( const char* key )
{
  size_t        len = NVSBUFSIZE ;                      // Length of the string

  nvsopen() ;                                           // Be sure to open nvs
  nvserr = nvs_get_str ( nvshandle, key, NULL, &len ) ; // Get length of contents
  return ( nvserr == ESP_OK ) ;                         // Return true if found
}


//**************************************************************************************************
//                                      T F T S E T                                                *
//**************************************************************************************************
// Request to display a segment on TFT.  Version for char* and String parameter.                   *
//**************************************************************************************************
void tftset ( uint16_t inx, const char *str )
{
  if ( inx < TFTSECS )                                  // Segment available on display
  {
    if ( str )                                          // String specified?
    {
      tftdata[inx].str = String ( str ) ;               // Yes, set string
    }
    tftdata[inx].update_req = true ;                    // and request flag
  }
}
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
void loop()
{// vs1053player->getBands() ;  
  VuUpdate();
  
  mp3loop() ;                                       // Do mp3 related actions
  if ( updatereq )                                  // Software update requested?
  {
    if ( displaytype == T_NEXTION )                 // NEXTION in use?
    {
      update_software ( "lstmodn",                  // Yes, update NEXTION image from remote image
                        UPDATEHOST, TFTFILE ) ;
    }
    update_software ( "lstmods",                    // Update sketch from remote file
                      UPDATEHOST, BINFILE ) ;
    resetreq = true ;                               // And reset
  }
  if ( resetreq )                                   // Reset requested?
  {
    delay ( 1000 ) ;                                // Yes, wait some time
    ESP.restart() ;                                 // Reboot
  }
  scanserial() ;                                    // Handle serial input
  scanserial2() ;                                   // Handle serial input from NEXTION (if active)
  scandigital() ;                                   // Scan digital inputs
  scanIR() ;                                        // See if IR input
  ArduinoOTA.handle() ;                             // Check for OTA
  mp3loop() ;                                       // Do more mp3 related actions
  handlehttpreply() ;
  cmdclient = cmdserver.available() ;               // Check Input from client?
  if ( cmdclient )                                  // Client connected?
  {
    dbgprint ( "Command client available" ) ;
    handlehttp() ;
  }
  // Handle MQTT.
  if ( mqtt_on )
  {
    mqttclient.loop() ;                             // Handling of MQTT connection
  }
  handleSaveReq() ;                                 // See if time to save settings
  handleIpPub() ;                                   // See if time to publish IP
  handleVolPub() ;                                  // See if time to publish volume
  chk_enc() ;                                       // Check rotary encoder functions
  check_CH376() ;                                   // Check Flashdrive insert/remove
}


//**************************************************************************************************
//                                    C H K H D R L I N E                                          *
//**************************************************************************************************
// Check if a line in the header is a reasonable headerline.                                       *
// Normally it should contain something like "icy-xxxx:abcdef".                                    *
//**************************************************************************************************
bool chkhdrline ( const char* str )
{
  char    b ;                                         // Byte examined
  int     len = 0 ;                                   // Lengte van de string

  while ( ( b = *str++ ) )                            // Search to end of string
  {
    len++ ;                                           // Update string length
    if ( ! isalpha ( b ) )                            // Alpha (a-z, A-Z)
    {
      if ( b != '-' )                                 // Minus sign is allowed
      {
        if ( b == ':' )                               // Found a colon?
        {
          return ( ( len > 5 ) && ( len < 50 ) ) ;    // Yes, okay if length is okay
        }
        else
        {
          return false ;                              // Not a legal character
        }
      }
    }
  }
  return false ;                                      // End of string without colon
}


//**************************************************************************************************
//                            S C A N _ C O N T E N T _ L E N G T H                                *
//**************************************************************************************************
// If the line contains content-length information: set clength (content length counter).          *
//**************************************************************************************************
void scan_content_length ( const char* metalinebf )
{
  if ( strstr ( metalinebf, "Content-Length" ) )        // Line contains content length
  {
    clength = atoi ( metalinebf + 15 ) ;                // Yes, set clength
    dbgprint ( "Content-Length is %d", clength ) ;      // Show for debugging purposes
  }
}


//**************************************************************************************************
//                                   H A N D L E B Y T E _ C H                                     *
//**************************************************************************************************
// Handle the next byte of data from server.                                                       *
// Chunked transfer encoding aware. Chunk extensions are not supported.                            *
//**************************************************************************************************
void handlebyte_ch ( uint8_t b )
{
  static int       chunksize = 0 ;                      // Chunkcount read from stream
  static uint16_t  playlistcnt ;                        // Counter to find right entry in playlist
  static int       LFcount ;                            // Detection of end of header
  static bool      ctseen = false ;                     // First line of header seen or not

  if ( chunked &&
       ( datamode & ( DATA |                           // Test op DATA handling
                      METADATA |
                      PLAYLISTDATA ) ) )
  {
    if ( chunkcount == 0 )                             // Expecting a new chunkcount?
    {
      if ( b == '\r' )                                 // Skip CR
      {
        return ;
      }
      else if ( b == '\n' )                            // LF ?
      {
        chunkcount = chunksize ;                       // Yes, set new count
        chunksize = 0 ;                                // For next decode
        return ;
      }
      // We have received a hexadecimal character.  Decode it and add to the result.
      b = toupper ( b ) - '0' ;                        // Be sure we have uppercase
      if ( b > 9 )
      {
        b = b - 7 ;                                    // Translate A..F to 10..15
      }
      chunksize = ( chunksize << 4 ) + b ;
      return  ;
    }
    chunkcount-- ;                                     // Update count to next chunksize block
  }
  if ( datamode == DATA )                              // Handle next byte of MP3/Ogg data
  {
    *outqp++ = b ;
    if ( outqp == ( outchunk.buf + sizeof(outchunk.buf) ) ) // Buffer full?
    {
      // Send data to playtask queue.  If the buffer cannot be placed within 200 ticks,
      // the queue is full, while the sender tries to send more.  The chunk will be dis-
      // carded it that case.
      xQueueSend ( dataqueue, &outchunk, 200 ) ;       // Send to queue
      outqp = outchunk.buf ;                           // Item empty now
    }
    if ( metaint )                                     // No METADATA on Ogg streams or mp3 files
    {
      if ( --datacount == 0 )                          // End of datablock?
      {
        setdatamode ( METADATA ) ;
        metalinebfx = -1 ;                             // Expecting first metabyte (counter)
      }
    }
    return ;
  }
  if ( datamode == INIT )                              // Initialize for header receive
  {
    ctseen = false ;                                   // Contents type not seen yet
    metaint = 0 ;                                      // No metaint found
    LFcount = 0 ;                                      // For detection end of header
    bitrate = 0 ;                                      // Bitrate still unknown
    dbgprint ( "Switch to HEADER" ) ;
    setdatamode ( HEADER ) ;                           // Handle header
    totalcount = 0 ;                                   // Reset totalcount
    metalinebfx = 0 ;                                  // No metadata yet
    metalinebf[0] = '\0' ;
  }
  if ( datamode == HEADER )                            // Handle next byte of MP3 header
  {
    if ( ( b > 0x7F ) ||                               // Ignore unprintable characters
         ( b == '\r' ) ||                              // Ignore CR
         ( b == '\0' ) )                               // Ignore NULL
    {
      // Yes, ignore
    }
    else if ( b == '\n' )                              // Linefeed ?
    {
      LFcount++ ;                                      // Count linefeeds
      metalinebf[metalinebfx] = '\0' ;                 // Take care of delimiter
      if ( chkhdrline ( metalinebf ) )                 // Reasonable input?
      {
        dbgprint ( "Headerline: %s",                   // Show headerline
                   metalinebf ) ;
        String metaline = String ( metalinebf ) ;      // Convert to string
        String lcml = metaline ;                       // Use lower case for compare
        lcml.toLowerCase() ;
        if ( lcml.startsWith ( "location: http://" ) ) // Redirection?
        {
          host = metaline.substring ( 17 ) ;           // Yes, get new URL
          hostreq = true ;                             // And request this one
        }
        if ( lcml.indexOf ( "content-type" ) >= 0)     // Line with "Content-Type: xxxx/yyy"
        {
          ctseen = true ;                              // Yes, remember seeing this
          String ct = metaline.substring ( 13 ) ;      // Set contentstype. Not used yet
          ct.trim() ;
          dbgprint ( "%s seen.", ct.c_str() ) ;
        }
        if ( lcml.startsWith ( "icy-br:" ) )
        {
          bitrate = metaline.substring(7).toInt() ;    // Found bitrate tag, read the bitrate
          if ( bitrate == 0 )                          // For Ogg br is like "Quality 2"
          {
            bitrate = 87 ;                             // Dummy bitrate
          }
        }
        else if ( lcml.startsWith ("icy-metaint:" ) )
        {
          metaint = metaline.substring(12).toInt() ;   // Found metaint tag, read the value
        }
        else if ( lcml.startsWith ( "icy-name:" ) )
        {
          icyname = metaline.substring(9) ;            // Get station name
          icyname.trim() ;                             // Remove leading and trailing spaces
          tftset ( 2, icyname ) ;                      // Set screen segment bottom part
          mqttpub.trigger ( MQTT_ICYNAME ) ;           // Request publishing to MQTT
        }
        else if ( lcml.startsWith ( "transfer-encoding:" ) )
        {
          // Station provides chunked transfer
          if ( lcml.endsWith ( "chunked" ) )
          {
            chunked = true ;                           // Remember chunked transfer mode
            chunkcount = 0 ;                           // Expect chunkcount in DATA
          }
        }
      }
      metalinebfx = 0 ;                                // Reset this line
      if ( ( LFcount == 2 ) && ctseen )                // Content type seen and a double LF?
      {
        dbgprint ( "Switch to DATA, bitrate is %d"     // Show bitrate
                   ", metaint is %d",                  // and metaint
                   bitrate, metaint ) ;
        setdatamode ( DATA ) ;                         // Expecting data now
        datacount = metaint ;                          // Number of bytes before first metadata
        queuefunc ( QSTARTSONG ) ;                     // Queue a request to start song
      }
    }
    else
    {
      metalinebf[metalinebfx++] = (char)b ;            // Normal character, put new char in metaline
      if ( metalinebfx >= METASIZ )                    // Prevent overflow
      {
        metalinebfx-- ;
      }
      LFcount = 0 ;                                    // Reset double CRLF detection
    }
    return ;
  }
  if ( datamode == METADATA )                          // Handle next byte of metadata
  {
    if ( metalinebfx < 0 )                             // First byte of metadata?
    {
      metalinebfx = 0 ;                                // Prepare to store first character
      metacount = b * 16 + 1 ;                         // New count for metadata including length byte
      if ( metacount > 1 )
      {
        dbgprint ( "Metadata block %d bytes",
                   metacount - 1 ) ;                   // Most of the time there are zero bytes of metadata
      }
    }
    else
    {
      metalinebf[metalinebfx++] = (char)b ;            // Normal character, put new char in metaline
      if ( metalinebfx >= METASIZ )                    // Prevent overflow
      {
        metalinebfx-- ;
      }
    }
    if ( --metacount == 0 )
    {
      metalinebf[metalinebfx] = '\0' ;                 // Make sure line is limited
      if ( strlen ( metalinebf ) )                     // Any info present?
      {
        // metaline contains artist and song name.  For example:
        // "StreamTitle='Don McLean - American Pie';StreamUrl='';"
        // Sometimes it is just other info like:
        // "StreamTitle='60s 03 05 Magic60s';StreamUrl='';"
        // Isolate the StreamTitle, remove leading and trailing quotes if present.
        showstreamtitle ( metalinebf ) ;               // Show artist and title if present in metadata
        mqttpub.trigger ( MQTT_STREAMTITLE ) ;         // Request publishing to MQTT
      }
      if ( metalinebfx  > ( METASIZ - 10 ) )           // Unlikely metaline length?
      {
        dbgprint ( "Metadata block too long! Skipping all Metadata from now on." ) ;
        metaint = 0 ;                                  // Probably no metadata
      }
      datacount = metaint ;                            // Reset data count
      //bufcnt = 0 ;                                   // Reset buffer count
      setdatamode ( DATA ) ;                           // Expecting data
    }
  }
  if ( datamode == PLAYLISTINIT )                      // Initialize for receive .m3u file
  {
    // We are going to use metadata to read the lines from the .m3u file
    // Sometimes this will only contain a single line
    metalinebfx = 0 ;                                  // Prepare for new line
    LFcount = 0 ;                                      // For detection end of header
    if ( localfile )                                   // SD-card mode?
    {
      setdatamode ( PLAYLISTDATA ) ;                   // Yes, no header here
    }
    else
    {
      setdatamode ( PLAYLISTHEADER ) ;                 // Handle playlist header
    }
    playlistcnt = 1 ;                                  // Reset for compare
    totalcount = 0 ;                                   // Reset totalcount
    clength = 0xFFFFFFFF ;                             // Content-length unknown
    dbgprint ( "Read from playlist" ) ;
  }
  if ( datamode == PLAYLISTHEADER )                    // Read header
  {
    if ( ( b > 0x7F ) ||                               // Ignore unprintable characters
         ( b == '\r' ) ||                              // Ignore CR
         ( b == '\0' ) )                               // Ignore NULL
    {
      return ;                                         // Quick return
    }
    else if ( b == '\n' )                              // Linefeed ?
    {
      LFcount++ ;                                      // Count linefeeds
      metalinebf[metalinebfx] = '\0' ;                 // Take care of delimeter
      dbgprint ( "Playlistheader: %s",                 // Show playlistheader
                 metalinebf ) ;
      scan_content_length ( metalinebf ) ;             // Check if it is a content-length line
      metalinebfx = 0 ;                                // Ready for next line
      if ( LFcount == 2 )
      {
        dbgprint ( "Switch to PLAYLISTDATA, "          // For debug
                   "search for entry %d",
                   playlist_num ) ;
        setdatamode ( PLAYLISTDATA ) ;                 // Expecting data now
        mqttpub.trigger ( MQTT_PLAYLISTPOS ) ;         // Playlistposition to MQTT
        return ;
      }
    }
    else
    {
      metalinebf[metalinebfx++] = (char)b ;            // Normal character, put new char in metaline
      if ( metalinebfx >= METASIZ )                    // Prevent overflow
      {
        metalinebfx-- ;
      }
      LFcount = 0 ;                                    // Reset double CRLF detection
    }
  }
  if ( datamode == PLAYLISTDATA )                      // Read next byte of .m3u file data
  {
    clength-- ;                                        // Decrease content length by 1
    if ( ( b > 0x7F ) ||                               // Ignore unprintable characters
         ( b == '\r' ) ||                              // Ignore CR
         ( b == '\0' ) )                               // Ignore NULL
    {
      // Yes, ignore
    }
    if ( b != '\n' )                                   // Linefeed?
    { // No, normal character in playlistdata,
      metalinebf[metalinebfx++] = (char)b ;            // add it to metaline
      if ( metalinebfx >= METASIZ )                    // Prevent overflow
      {
        metalinebfx-- ;
      }
    }
    if ( ( b == '\n' ) ||                              // linefeed ?
         ( clength == 0 ) )                            // Or end of playlist data contents
    {
      int inx ;                                        // Pointer in metaline
      metalinebf[metalinebfx] = '\0' ;                 // Take care of delimeter
      dbgprint ( "Playlistdata: %s",                   // Show playlistheader
                 metalinebf ) ;
      if ( strlen ( metalinebf ) < 5 )                 // Skip short lines
      {
        metalinebfx = 0 ;                              // Flush line
        metalinebf[0] = '\0' ;
        return ;
      }
      String metaline = String ( metalinebf ) ;        // Convert to string
      if ( metaline.indexOf ( "#EXTINF:" ) >= 0 )      // Info?
      {
        if ( playlist_num == playlistcnt )             // Info for this entry?
        {
          inx = metaline.indexOf ( "," ) ;             // Comma in this line?
          if ( inx > 0 )
          {
            // Show artist and title if present in metadata
            showstreamtitle ( metaline.substring ( inx + 1 ).c_str(), true ) ;
            mqttpub.trigger ( MQTT_STREAMTITLE ) ;     // Request publishing to MQTT
          }
        }
      }
      if ( metaline.startsWith ( "#" ) )               // Commentline?
      {
        metalinebfx = 0 ;                              // Yes, ignore
        return ;                                       // Ignore commentlines
      }
      // Now we have an URL for a .mp3 file or stream.  Is it the rigth one?
      dbgprint ( "Entry %d in playlist found: %s", playlistcnt, metalinebf ) ;
      if ( playlist_num == playlistcnt  )
      {
        inx = metaline.indexOf ( "http://" ) ;         // Search for "http://"
        if ( inx >= 0 )                                // Does URL contain "http://"?
        {
          host = metaline.substring ( inx + 7 ) ;      // Yes, remove it and set host
        }
        else
        {
          host = metaline ;                            // Yes, set new host
        }
        if ( localfile )                               // SD card mode?
        {
          if ( ! metaline.startsWith ( "localhost" ) ) // Prepend "localhost" if missing
          {
            host = String ( "localhost/" ) + metaline ;
          }
          if ( ! connecttofile() )                     // Yes, connect to file
          {
            setdatamode ( STOPPED ) ;                  // Error, stop!
          }
        }
        else
        {
          connecttohost() ;                           // Connect to stream host
        }
      }
      metalinebfx = 0 ;                                // Prepare for next line
      host = playlist ;                                // Back to the .m3u host
      playlistcnt++ ;                                  // Next entry in playlist
    }
  }
}


//**************************************************************************************************
//                                     G E T C O N T E N T T Y P E                                 *
//**************************************************************************************************
// Returns the contenttype of a file to send.                                                      *
//**************************************************************************************************
String getContentType ( String filename )
{
  if      ( filename.endsWith ( ".html" ) ) return "text/html" ;
  else if ( filename.endsWith ( ".png"  ) ) return "image/png" ;
  else if ( filename.endsWith ( ".gif"  ) ) return "image/gif" ;
  else if ( filename.endsWith ( ".jpg"  ) ) return "image/jpeg" ;
  else if ( filename.endsWith ( ".ico"  ) ) return "image/x-icon" ;
  else if ( filename.endsWith ( ".css"  ) ) return "text/css" ;
  else if ( filename.endsWith ( ".zip"  ) ) return "application/x-zip" ;
  else if ( filename.endsWith ( ".gz"   ) ) return "application/x-gzip" ;
  else if ( filename.endsWith ( ".mp3"  ) ) return "audio/mpeg" ;
  else if ( filename.endsWith ( ".pw"   ) ) return "" ;              // Passwords are secret
  return "text/plain" ;
}


//**************************************************************************************************
//                                        H A N D L E F S F                                        *
//**************************************************************************************************
// Handling of requesting pages from the PROGMEM. Example: favicon.ico                             *
//**************************************************************************************************
void handleFSf ( const String& pagename )
{
  String                 ct ;                           // Content type
  const char*            p ;
  int                    l ;                            // Size of requested page
  int                    TCPCHUNKSIZE = 1024 ;          // Max number of bytes per write

  dbgprint ( "FileRequest received %s", pagename.c_str() ) ;
  ct = getContentType ( pagename ) ;                    // Get content type
  if ( ( ct == "" ) || ( pagename == "" ) )             // Empty is illegal
  {
    cmdclient.println ( "HTTP/1.1 404 Not Found" ) ;
    cmdclient.println ( "" ) ;
    return ;
  }
  else
  {
    if ( pagename.indexOf ( "index.html" ) >= 0 )       // Index page is in PROGMEM
    {
      p = index_html ;
      l = sizeof ( index_html ) ;
    }
    else if ( pagename.indexOf ( "radio.css" ) >= 0 )   // CSS file is in PROGMEM
    {
      p = radio_css + 1 ;
      l = sizeof ( radio_css ) ;
    }
    else if ( pagename.indexOf ( "config.html" ) >= 0 ) // Config page is in PROGMEM
    {
      p = config_html ;
      l = sizeof ( config_html ) ;
    }
    else if ( pagename.indexOf ( "mp3play.html" ) >= 0 ) // Mp3player page is in PROGMEM
    {
      p = mp3play_html ;
      l = sizeof ( mp3play_html ) ;
    }
    else if ( pagename.indexOf ( "about.html" ) >= 0 )  // About page is in PROGMEM
    {
      p = about_html ;
      l = sizeof ( about_html ) ;
    }
    else if ( pagename.indexOf ( "favicon.ico" ) >= 0 ) // Favicon icon is in PROGMEM
    {
      p = (char*)favicon_ico ;
      l = sizeof ( favicon_ico ) ;
    }

    else if ( pagename.indexOf ( "Intro.png" ) >= 0 ) // Favicon icon is in PROGMEM
    {
      p = (char*)IntroBitmap ;
      l = sizeof ( IntroBitmap ) ;
    }
 
    else if ( pagename.indexOf ( "find.html" ) >= 0 ) // find pafe is in PROGMEM
    {
      p = find_html ;
      l = sizeof ( find_html ) ;
    } 
    else
    {
      p = index_html ;
      l = sizeof ( index_html ) ;
    }
    if ( *p == '\n' )                                   // If page starts with newline:
    {
      p++ ;                                             // Skip first character
      l-- ;
    }
    dbgprint ( "Length of page is %d", strlen ( p ) ) ;
    cmdclient.print ( httpheader ( ct ) ) ;             // Send header
    // The content of the HTTP response follows the header:
    if ( l < 10 )
    {
      cmdclient.println ( "Testline<br>" ) ;
    }
    else
    {
      while ( l )                                       // Loop through the output page
      {
        if ( l <= TCPCHUNKSIZE )                        // Near the end?
        {
          cmdclient.write ( p, l ) ;                    // Yes, send last part
          l = 0 ;
        }
        else
        {
          cmdclient.write ( p, TCPCHUNKSIZE ) ;         // Send part of the page
          p += TCPCHUNKSIZE ;                           // Update startpoint and rest of bytes
          l -= TCPCHUNKSIZE ;
        }
      }
    }
    // The HTTP response ends with another blank line:
    cmdclient.println() ;
    dbgprint ( "Response send" ) ;
  }
}


//**************************************************************************************************
//                                         C H O M P                                               *
//**************************************************************************************************
// Do some filtering on de inputstring:                                                            *
//  - String comment part (starting with "#").                                                     *
//  - Strip trailing CR.                                                                           *
//  - Strip leading spaces.                                                                        *
//  - Strip trailing spaces.                                                                       *
//**************************************************************************************************
void chomp ( String &str )
{
  int   inx ;                                         // Index in de input string

  if ( ( inx = str.indexOf ( "#" ) ) >= 0 )           // Comment line or partial comment?
  {
    str.remove ( inx ) ;                              // Yes, remove
  }
  str.trim() ;                                        // Remove spaces and CR
}


//**************************************************************************************************
//                                     A N A L Y Z E C M D                                         *
//**************************************************************************************************
// Handling of the various commands from remote webclient, Serial or MQTT.                         *
// Version for handling string with: <parameter>=<value>                                           *
//**************************************************************************************************
const char* analyzeCmd ( const char* str )
{
  char*        value ;                           // Points to value after equalsign in command
  const char*  res ;                             // Result of analyzeCmd

  value = strstr ( str, "=" ) ;                  // See if command contains a "="
  if ( value )
  {
    *value = '\0' ;                              // Separate command from value
    res = analyzeCmd ( str, value + 1 ) ;        // Analyze command and handle it
    *value = '=' ;                               // Restore equal sign
  }
  else
  {
    res = analyzeCmd ( str, "0" ) ;              // No value, assume zero
  }
  return res ;
}


//**************************************************************************************************
//                                     A N A L Y Z E C M D                                         *
//**************************************************************************************************
// Handling of the various commands from remote webclient, serial or MQTT.                         *
// par holds the parametername and val holds the value.                                            *
// "wifi_00" and "preset_00" may appear more than once, like wifi_01, wifi_02, etc.                *
// Examples with available parameters:                                                             *
//   preset     = 12                        // Select start preset to connect to                   *
//   preset_00  = <mp3 stream>              // Specify station for a preset 00-max *)              *
//   volume     = 95                        // Percentage between 0 and 100                        *
//   upvolume   = 2                         // Add percentage to current volume                    *
//   downvolume = 2                         // Subtract percentage from current volume             *
//   toneha     = <0..15>                   // Setting treble gain                                 *
//   tonehf     = <0..15>                   // Setting treble frequency                            *
//   tonela     = <0..15>                   // Setting bass gain                                   *
//   tonelf     = <0..15>                   // Setting treble frequency                            *
//   station    = <mp3 stream>              // Select new station (will not be saved)              *
//   station    = <URL>.mp3                 // Play standalone .mp3 file (not saved)               *
//   station    = <URL>.m3u                 // Select playlist (will not be saved)                 *
//   stop                                   // Stop playing                                        *
//   resume                                 // Resume playing                                      *
//   mute                                   // Mute/unmute the music (toggle)                      *
//   wifi_00    = mySSID/mypassword         // Set WiFi SSID and password *)                       *
//   mqttbroker = mybroker.com              // Set MQTT broker to use *)                           *
//   mqttprefix = XP93g                     // Set MQTT broker to use                              *
//   mqttport   = 1883                      // Set MQTT port to use, default 1883 *)               *
//   mqttuser   = myuser                    // Set MQTT user for authentication *)                 *
//   mqttpasswd = mypassword                // Set MQTT password for authentication *)             *
//   clk_server = pool.ntp.org              // Time server to be used *)                           *
//   clk_offset = <-11..+14>                // Offset with respect to UTC in hours *)              *
//   clk_dst    = <1..2>                    // Offset during daylight saving time in hours *)      *
//   mp3track   = <nodeID>                  // Play track from SD card, nodeID 0 = random          *
//   settings                               // Returns setting like presets and tone               *
//   status                                 // Show current URL to play                            *
//   test                                   // For test purposes                                   *
//   debug      = 0 or 1                    // Switch debugging on or off                          *
//   reset                                  // Restart the ESP32                                   *
//   bat0       = 2318                      // ADC value for an empty battery                      *
//   bat100     = 2916                      // ADC value for a fully charged battery               *
//   fs         = USB or SD                 // Select local filesystem for MP# player mode.        *
//  Commands marked with "*)" are sensible during initialization only                              *
//**************************************************************************************************
const char* analyzeCmd ( const char* par, const char* val )
{
  String             argument ;                       // Argument as string
  String             value ;                          // Value of an argument as a string
  String             value2;                         //mark
  String             piclink;                         //mark
  String             statname;                         //mark
  String             staturl;                         //mark
  String             statnum;                         //mark
   String             statnum2;                         //mark 
  int                ivalue ;                         // Value of argument as an integer
  static char        reply[180] ;                     // Reply to client, will be returned
  uint8_t            oldvol ;                         // Current volume
  bool               relative ;                       // Relative argument (+ or -)
  String             tmpstr ;                         // Temporary for value
  uint32_t           av ;                             // Available in stream/file
  char                tmp;                            //mark
  String             urltemp[200];                         // added by mark
  String             StationPresetnbr;                 // added by mark
  String             StationNme[100];                       // added by mark
  String             Setstatimg;                      // added by mark
  String             Setstat;                      // added by mark
  int                inxtmp;                     // added by mark
  int                inxtmp2;                     // added by mark
  int                cnttmp;                    // added by mark
  blset ( true ) ;                                    // Enable backlight of TFT
  strcpy ( reply, "Command accepted" ) ;              // Default reply
  argument = String ( par ) ;                         // Get the argument
  chomp ( argument ) ;                                // Remove comment and useless spaces
  if ( argument.length() == 0 )                       // Lege commandline (comment)?
  {
    return reply ;                                    // Ignore
  }
  argument.toLowerCase() ;                            // Force to lower case
  value = String ( val ) ;                            // Get the specified value
  //value2 = String ( val ) ;
  chomp ( value ) ;                                   // Remove comment and extra spaces
  ivalue = value.toInt() ;                            // Also as an integer
  ivalue = abs ( ivalue ) ;                           // Make positive
  relative = argument.indexOf ( "up" ) == 0 ;         // + relative setting?
  if ( argument.indexOf ( "down" ) == 0 )             // - relative setting?
  {
    relative = true ;                                 // It's relative
    ivalue = - ivalue ;                               // But with negative value
  }
  if ( value.startsWith ( "http://" ) )               // Does (possible) URL contain "http://"?
  {
    value.remove ( 0, 7 ) ;                           // Yes, remove it
  }
  if ( value.length() )
  {
    tmpstr = value ;                                  // Make local copy of value
    if ( argument.indexOf ( "passw" ) >= 0 )          // Password in value?
    {
      tmpstr = String ( "*******" ) ;                 // Yes, hide it
    }
    dbgprint ( "Command: %s with parameter %s",
               argument.c_str(), tmpstr.c_str() ) ;
  }
  else
  {
    dbgprint ( "Command: %s (without parameter)",
               argument.c_str() ) ;
  }
  if ( argument.indexOf ( "volume" ) >= 0 )           // Volume setting?
  {
    // Volume may be of the form "upvolume", "downvolume" or "volume" for relative or absolute setting
    oldvol = vs1053player->getVolume() ;              // Get current volume
    if ( relative )                                   // + relative setting?
    {
      ini_block.reqvol = oldvol + ivalue ;            // Up/down by 0.5 or more dB
    }
    else
    {
      ini_block.reqvol = ivalue ;                     // Absolue setting
    }
    if ( ini_block.reqvol > 127 )                     // Wrapped around?
    {
      ini_block.reqvol = 0 ;                          // Yes, keep at zero
    }
    if ( ini_block.reqvol > 100 )
    {
      ini_block.reqvol = 100 ;                        // Limit to normal values
    }
    muteflag = false ;                                // Stop possibly muting
    sprintf ( reply, "Volume is now %d",              // Reply new volume
              ini_block.reqvol ) ;
  }
  else if ( argument == "mute" )                      // Mute/unmute request
  {
    muteflag = !muteflag ;                            // Request volume to zero/normal
  }
  else if ( argument.indexOf ( "ir_" ) >= 0 )         // Ir setting?
  { // Do not handle here
  }
  else if ( argument.indexOf ( "preset_" ) >= 0 )     // Enumerated preset?
  { // Do not handle here
  }
  else if ( argument.indexOf ( "preset" ) >= 0 )      // (UP/DOWN)Preset station?
  {
    // If MP3 player is active: change track
    if ( localfile &&
         ( ( datamode & DATA ) != 0 ) &&              // MP# player active?
         relative )
    {
      setdatamode ( STOPREQD ) ;                      // Force stop MP3 player
      if ( playlist_num )                             // In playlist mode?
      {
        playlist_num += ivalue ;                      // Set new entry number
        if ( playlist_num <= 0 )                      // Limit number
        {
          playlist_num = 1 ;
        }
        host = playlist ;                             // Yes, prepare to read playlist
      }
      else
      {
        tmpstr = selectnextFSnode ( ivalue ) ;        // Select the next or previous file on SD/USB
        host = getFSfilename ( tmpstr ) ;
        sprintf ( reply, "Playing %s",                // Reply new filename
                  host.c_str() ) ;
      }
      hostreq = true ;                                // Request this host
    }
    else
    {
      if ( relative )                                 // Relative argument?
      {
        currentpreset = ini_block.newpreset ;         // Remember currentpreset
        ini_block.newpreset += ivalue ;               // Yes, adjust currentpreset
      }
      else
      {
        ini_block.newpreset = ivalue ;                // Otherwise set station
        playlist_num = 0 ;                            // Absolute, reset playlist
        currentpreset = -1 ;                          // Make sure current is different
      }
      setdatamode ( STOPREQD ) ;                      // Force stop MP3 player
      sprintf ( reply, "Preset is now %d",            // Reply new preset
                ini_block.newpreset ) ;
    }
  }
  else if ( argument == "stop" )                      // (un)Stop requested?
  {
    if ( datamode & ( HEADER | DATA | METADATA | PLAYLISTINIT |
                      PLAYLISTHEADER | PLAYLISTDATA ) )

    {
      setdatamode ( STOPREQD ) ;                      // Request STOP
    }
    else
    {
      hostreq = true ;                                // Request UNSTOP
    }
  }
  else if ( ( value.length() > 0 ) &&
            ( ( argument == "mp3track" ) ||           // Select a track from SD card?
              ( argument == "station" ) ) )           // Station in the form address:port
  {
    if ( argument.startsWith ( "mp3" ) )              // MP3 track to search for
    {
      value = getFSfilename ( value ) ;               // like "localhost/........"
      if ( value.length() == 0 )                      // Found?
      {
        strcpy ( reply, "Command not accepted!" ) ;   // No, error reply
        return reply ;
      }
    }
    if ( datamode & ( HEADER | DATA | METADATA | PLAYLISTINIT |
                      PLAYLISTHEADER | PLAYLISTDATA ) )
    {
      setdatamode ( STOPREQD ) ;                      // Request STOP
    }
    host = value ;                                    // Save it for storage and selection later
    hostreq = true ;                                  // Force this station as new preset
    sprintf ( reply,
              "Playing %s",                           // Format reply
              host.c_str() ) ;
    utf8ascii_ip ( reply ) ;                          // Remove possible strange characters
  }
  else if ( argument == "status" )                    // Status request
  {
    if ( datamode == STOPPED )
    {
      sprintf ( reply, "Player stopped" ) ;           // Format reply
    }
    else
    {
      sprintf ( reply, "%s - %s", icyname.c_str(),
                icystreamtitle.c_str() ) ;            // Streamtitle from metadata
    }
  }
  else if ( argument.startsWith ( "reset" ) )         // Reset request
  {
    resetreq = true ;                                 // Reset all
  }
  else if ( argument.startsWith ( "update" ) )        // Update request
  {
    updatereq = true ;                                // Reset all
  }
  
  else if ( argument.startsWith ( "hostplaying" ) )        // Update request
  {
     // When someone opens a new browser to connect to the webserver, radio data and icon are not visible.
     // Because the webserver needs to fetch data to display first
   //  sprintf ( reply, "now playing:=%s", host.c_str()) ; // this gives the actual URL playing  
   // value2= String (currentpreset);
     sprintf ( reply, "precon_0%s", String(currentpreset)) ;
    
    nvsopen();
   // value="precon_0"+tmpstr;
    value2=nvsgetstr ( reply );
         sprintf ( reply, "%s",value2.c_str());
    
    // dbgprint("preset: %s",currentpreset);
     //currentpreset
     /*
     nvsopen(); // make sure the NVS is accessible
     for (cnttmp=0;cnttmp<8;cnttmp++)
     {
      sprintf(reply,"preset_0%d",cnttmp);
      value2= nvsgetstr (reply);
      dbgprint("%s",value2.c_str());
      // now lets find out if it contains our host
      dbgprint("host=%s",host.c_str());
      value= value2.indexOf(host.c_str());
      dbgprint("gevonden:%s",value);
     }
     */
  }
  
  else if ( argument.startsWith ( "setmem" ) )        // Update request
  { 

    value2=value; 
    value2.remove ( 1, value2.length() ) ;// bevat nu station nummer
    statnum="preset_0"+value2;//iets mee doen
    statnum2=value2;
    value2=value;  //1__stationname_url_=stationURL_icon_=favicon
    value2.remove(0,3); // stationname_url_=stationURL_icon_=favicon
    value2.remove(value2.indexOf("_url_="),value2.length()-value2.indexOf("_url_=")); //stationname
    statname=value2;
  
    value2=value;    //1__stationname_url_=stationURL_icon_=favicon
    value2.remove(value2.indexOf("_icon_="),value2.length()-value2.indexOf("_icon_=") );//1__stationname_url_=stationURL
            
    value2.remove(0, value2.indexOf("_url_=")+6); //stationURL
    inxtmp=value2.indexOf ( "http://" ) ;         // Search for "http://"
    inxtmp2=value2.indexOf ( "https://" ) ;         // Search for "https://"
    if ( inxtmp >= 0 )                                // Does URL contain "http://"?
    {
     staturl = value2.substring ( inxtmp + 7 ) ;      // Yes, remove it and set host
    }
    else if (inxtmp2 >=0)
    {
     staturl = value2.substring ( inxtmp2 + 8 ) ; // Yes, remove it and set host
    }
    else
    {
    staturl=value2;   // none of the above, no need to remove anything
    }

    
    
    value2=value;//1__stationname_url_=stationURL_icon_=favicon
    value2.remove(0,value2.indexOf("_icon_=")+7);//favicon
    piclink=value2;
     sprintf ( reply, "O yeah command setmemt=%s", value2.c_str()) ;
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
