donnersm/EdisonRadio/ArduinoSketch/MainProgram/ESP32_Radio/_dragon.h

#define INTRO_WIDTH 110
#define INTRO_HEIGHT 70

const PROGMEM uint16_t IntroBitmap[INTRO_WIDTH * INTRO_HEIGHT] = {
    0XFFFF, 0XFFFF, 0XFFFF, 0XFFFF, 0XFFFF, 0XFFFF, 0XFFFF, 0XFFFF, 0XFFFF,
    0XFFFF, 0XFFFF, 0XFFFF, 0XFFFF, 0XFFFF, 0XFFFF, 0XFFFF, 0XFFFF, 0XFFFF,
    0XFFFF, 0XFFFF, 0XFFFF, 0XFFFF, 0XFFFF, 0XFFFF, 0XFFFF, 0XFFFF, 0XFFFF,
    0XFFFF, 0XFFFF, 0XFFFF, 0XFFFF, 0XFFFF, 0XFFFF, 0XFFFF, 0XFFFF, 0XFFFF,
    0XFFFF, 0XFFFF, 0XFFFF, 0XFFFF, 0XFFFF, 0XFFFF, 0XFFFF, 0XFFFF, 0XFFFF,
    0XFFFF, 0XFFFF, 0XFFFF, 0XFFFF, 0XFFFF, 0XFFFF, 0XFFFF, 0XFFFF, 0XFFFF,
    0XFFFF, 0XFFFF, 0XFFFF, 0XFFFF, 0XFFFF, 0XFFFF, 0XFFFF, 0XFFFF, 0XFFFF,
    0XFFFF, 0XFFFF, 0XFFFF, 0XFFFF, 0XFFFF, 0XFFFF, 0XFFFF, 0XFFFF, 0XFFFF,
    0XFFFF, 0XFFFF, 0XFFFF, 0XFFFF, 0XFFFF, 0XFFFF, 0XFFFF, 0XFFFF, 0XFFFF,
    0XFFFF, 0XFFFF, 0XFFFF, 0XFFFF, 0XFFFF, 0XFFFF, 0XFFFF, 0XFFFF, 0XFFFF,
    0XFFFF, 0XFFFF, 0XFFFF, 0XFFFF, 0XFFFF, 0XFFFF, 0XFFFF, 0XFFFF, 0XFFFF,
    0XFFFF, 0XFFFF, 0XFFFF, 0XFFFF, 0XFFFF, 0XFFFF, 0XFFFF, 0XFFFF, 0XFFFF,
    0XFFFF, 0XFFFF, 0XFFFF, 0XFFFF, 0XFFFF, 0XFFFF, 0XFFFF, 0XFFFF, 0XFFFF,
    0XFFFF, 0XFFFF, 0XFFFF, 0XFFFF, 0XFFFF, 0XFFFF, 0XFFFF, 0XFFFF, 0XFFFF,
    0XFFFF, 0XFFFF, 0XFFFF, 0XFFFF, 0XFFFF, 0XFFFF, 0XFFFF, 0XFFFF, 0XFFFF,
    0XFFFF, 0XFFFF, 0XFFFF, 0XFFFF, 0XFFFF, 0XFFFF, 0XFFFF, 0XFFFF, 0XFFFF,
    0XFFFF, 0XFFFF, 0XFFFF, 0XFFFF, 0XFFFF, 0XFFFF, 0XFFFF, 0XFFFF, 0XFFFF,
    0XFFFF, 0XFFFF, 0XFFFF, 0XFFFF, 0XFFFF, 0XFFFF, 0XFFFF, 0XFFFF, 0XFFFF,
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
    0X0547, 0X0547, 0X0547, 0X0547, 0X0547, 0X0547, 0X0547, 0X0547, 0X0547,
    0X0547, 0X0547, 0X0547, 0X0547, 0X0547, 0X0547, 0X0547, 0X0547, 0X0547,
    0X0547, 0X0547, 0X0547, 0X0547, 0X0547, 0X0547, 0X0547, 0X0547, 0X0547,
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
