donnersm/EdisonRadio/ArduinoSketch/MainProgram/ESP32_Radio/patches.h

//const unsigned short analizer[1000] PROGMEM = { /* Compressed plugin */
#define ANALIZER_SIZE 1000
const unsigned short analizer[1000] = { /* Compressed plugin */
        0x0007, 0x0001, 0x8d00, 0x0006, 0x0004, 0x2803, 0x5b40, 0x0000, /*    0 */
        0x0024, 0x0007, 0x0001, 0x8d02, 0x0006, 0x00d6, 0x3e12, 0xb817, /*    8 */
        0x3e12, 0x3815, 0x3e05, 0xb814, 0x3615, 0x0024, 0x0000, 0x800a, /*   10 */
        0x3e10, 0x3801, 0x0006, 0x0800, 0x3e10, 0xb803, 0x0000, 0x0303, /*   18 */
        0x3e11, 0x3805, 0x3e11, 0xb807, 0x3e14, 0x3812, 0xb884, 0x130c, /*   20 */
        0x3410, 0x4024, 0x4112, 0x10d0, 0x4010, 0x008c, 0x4010, 0x0024, /*   28 */
        0xf400, 0x4012, 0x3000, 0x3840, 0x3009, 0x3801, 0x0000, 0x0041, /*   30 */
        0xfe02, 0x0024, 0x2903, 0xb480, 0x48b2, 0x0024, 0x36f3, 0x0844, /*   38 */
        0x6306, 0x8845, 0xae3a, 0x8840, 0xbf8e, 0x8b41, 0xac32, 0xa846, /*   40 */
        0xffc8, 0xabc7, 0x3e01, 0x7800, 0xf400, 0x4480, 0x6090, 0x0024, /*   48 */
        0x6090, 0x0024, 0xf400, 0x4015, 0x3009, 0x3446, 0x3009, 0x37c7, /*   50 */
        0x3009, 0x1800, 0x3009, 0x3844, 0x48b3, 0xe1e0, 0x4882, 0x4040, /*   58 */
        0xfeca, 0x0024, 0x5ac2, 0x0024, 0x5a52, 0x0024, 0x4cc2, 0x0024, /*   60 */
        0x48ba, 0x4040, 0x4eea, 0x4801, 0x4eca, 0x9800, 0xff80, 0x1bc1, /*   68 */
        0xf1eb, 0xe3e2, 0xf1ea, 0x184c, 0x4c8b, 0xe5e4, 0x48be, 0x9804, /*   70 */
        0x488e, 0x41c6, 0xfe82, 0x0024, 0x5a8e, 0x0024, 0x525e, 0x1b85, /*   78 */
        0x4ffe, 0x0024, 0x48b6, 0x41c6, 0x4dd6, 0x48c7, 0x4df6, 0x0024, /*   80 */
        0xf1d6, 0x0024, 0xf1d6, 0x0024, 0x4eda, 0x0024, 0x0000, 0x0fc3, /*   88 */
        0x2903, 0xb480, 0x4e82, 0x0024, 0x4084, 0x130c, 0x0006, 0x0500, /*   90 */
        0x3440, 0x4024, 0x4010, 0x0024, 0xf400, 0x4012, 0x3200, 0x4024, /*   98 */
        0xb132, 0x0024, 0x4214, 0x0024, 0xf224, 0x0024, 0x6230, 0x0024, /*   a0 */
        0x0001, 0x0001, 0x2803, 0x54c9, 0x0000, 0x0024, 0xf400, 0x40c2, /*   a8 */
        0x3200, 0x0024, 0xff82, 0x0024, 0x48b2, 0x0024, 0xb130, 0x0024, /*   b0 */
        0x6202, 0x0024, 0x003f, 0xf001, 0x2803, 0x57d1, 0x0000, 0x1046, /*   b8 */
        0xfe64, 0x0024, 0x48be, 0x0024, 0x2803, 0x58c0, 0x3a01, 0x8024, /*   c0 */
        0x3200, 0x0024, 0xb010, 0x0024, 0xc020, 0x0024, 0x3a00, 0x0024, /*   c8 */
        0x36f4, 0x1812, 0x36f1, 0x9807, 0x36f1, 0x1805, 0x36f0, 0x9803, /*   d0 */
        0x36f0, 0x1801, 0x3405, 0x9014, 0x36f3, 0x0024, 0x36f2, 0x1815, /*   d8 */
        0x2000, 0x0000, 0x36f2, 0x9817, 0x0007, 0x0001, 0x8d6d, 0x0006, /*   e0 */
        0x01f6, 0x3613, 0x0024, 0x3e12, 0xb817, 0x3e12, 0x3815, 0x3e05, /*   e8 */
        0xb814, 0x3645, 0x0024, 0x0000, 0x800a, 0x3e10, 0xb803, 0x3e11, /*   f0 */
        0x3805, 0x3e11, 0xb811, 0x3e14, 0xb813, 0x3e13, 0xf80e, 0x4182, /*   f8 */
        0x384d, 0x0006, 0x0912, 0x2803, 0x6105, 0x0006, 0x0451, 0x0006, /*  100 */
        0xc352, 0x3100, 0x8803, 0x6238, 0x1bcc, 0x0000, 0x0024, 0x2803, /*  108 */
        0x7705, 0x4194, 0x0024, 0x0006, 0x0912, 0x3613, 0x0024, 0x0006, /*  110 */
        0x0411, 0x0000, 0x0302, 0x3009, 0x3850, 0x0006, 0x0410, 0x3009, /*  118 */
        0x3840, 0x0000, 0x1100, 0x2914, 0xbec0, 0xb882, 0xb801, 0x0000, /*  120 */
        0x1000, 0x0006, 0x0810, 0x2915, 0x7ac0, 0xb882, 0x0024, 0x3900, /*  128 */
        0x9bc1, 0x0006, 0xc351, 0x3009, 0x1bc0, 0x3009, 0x1bd0, 0x3009, /*  130 */
        0x0404, 0x0006, 0x0451, 0x2803, 0x66c0, 0x3901, 0x0024, 0x4448, /*  138 */
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
};


// FINE PATCHES
